hi631/FLEX09/moni09/basic.asm

ROMBASE   EQU  $E000
UART      EQU  $FFD0
RECEV     EQU  UART+1
TRANS     EQU  UART+1
USTAT     EQU  UART
UCTRL     EQU  UART
RTS_LOW   EQU  $15

BS        EQU  8              BACKSPACE
CR        EQU  $D             ENTER KEY
ESC       EQU  $1B            ESCAPE CODE
SPACE     EQU  $20            SPACE (BLANK)
STKBUF    EQU  58             STACK BUFFER ROOM
LBUFMX    EQU  250            MAX NUMBER OF CHARS IN A BASIC LINE
MAXLIN    EQU  $FA            MAXIMUM MS BYTE OF LINE NUMBER
* PSEUDO OPS
SKP1      EQU  $21            OP CODE OF BRN    - SKIP ONE BYTE
SKP2      EQU  $8C            OP CODE OF CMPX # - SKIP TWO BYTES
SKP1LD    EQU  $86            OP CODE OF LDA #  - SKIP THE NEXT BYTE AND
*                             LOAD THE VALUE OF THAT BYTE INTO ACCA - USUALLY
*                             USED TO LOAD ACCA WITH A NON-ZERO VALUE

          ORG  0
ENDFLG    RMB  1              STOP/END FLAG: POSITIVE=STOP, NEG=END
CHARAC    RMB  1              TERMINATOR FLAG 1
ENDCHR    RMB  1              TERMINATOR FLAG 2
TMPLOC    RMB  1              SCRATCH VARIABLE
IFCTR     RMB  1              IF COUNTER - HOW MANY IF STATEMENTS IN A LINE
DIMFLG    RMB  1              *DV* ARRAY FLAG 0=EVALUATE, 1=DIMENSIONING
VALTYP    RMB  1              *DV* *PV TYPE FLAG: 0=NUMERIC, $FF=STRING
GARBFL    RMB  1              *TV STRING SPACE HOUSEKEEPING FLAG
ARYDIS    RMB  1              DISABLE ARRAY SEARCH: 00=ALLOW SEARCH
INPFLG    RMB  1              *TV INPUT FLAG: READ=0, INPUT<>0
RELFLG    RMB  1              *TV RELATIONAL OPERATOR FLAG
TEMPPT    RMB  2              *PV TEMPORARY STRING STACK POINTER
LASTPT    RMB  2              *PV ADDR OF LAST USED STRING STACK ADDRESS
TEMPTR    RMB  2              TEMPORARY POINTER
TMPTR1    RMB  2              TEMPORARY DESCRIPTOR STORAGE (STACK SEARCH)
FPA2      RMB  4              FLOATING POINT ACCUMULATOR #2 MANTISSA
BOTSTK    RMB  2              BOTTOM OF STACK AT LAST CHECK
TXTTAB    RMB  2              *PV BEGINNING OF BASIC PROGRAM
VARTAB    RMB  2              *PV START OF VARIABLES
ARYTAB    RMB  2              *PV START OF ARRAYS
ARYEND    RMB  2              *PV END OF ARRAYS (+1)
FRETOP    RMB  2              *PV START OF STRING STORAGE (TOP OF FREE RAM)
STRTAB    RMB  2              *PV START OF STRING VARIABLES
FRESPC    RMB  2              UTILITY STRING POINTER
MEMSIZ    RMB  2              *PV TOP OF STRING SPACE
OLDTXT    RMB  2              SAVED LINE NUMBER DURING A "STOP"
BINVAL    RMB  2              BINARY VALUE OF A CONVERTED LINE NUMBER
OLDPTR    RMB  2              SAVED INPUT PTR DURING A "STOP"
TINPTR    RMB  2              TEMPORARY INPUT POINTER STORAGE
DATTXT    RMB  2              *PV 'DATA' STATEMENT LINE NUMBER POINTER
DATPTR    RMB  2              *PV 'DATA' STATEMENT ADDRESS POINTER
DATTMP    RMB  2              DATA POINTER FOR 'INPUT' & 'READ'
VARNAM    RMB  2              *TV TEMP STORAGE FOR A VARIABLE NAME
VARPTR    RMB  2              *TV POINTER TO A VARIABLE DESCRIPTOR
VARDES    RMB  2              TEMP POINTER TO A VARIABLE DESCRIPTOR
RELPTR    RMB  2              POINTER TO RELATIONAL OPERATOR PROCESSING ROUTINE
TRELFL    RMB  1              TEMPORARY RELATIONAL OPERATOR FLAG BYTE
* FLOATING POINT ACCUMULATORS #3,4 & 5 ARE MOSTLY
* USED AS SCRATCH PAD VARIABLES.
** FLOATING POINT ACCUMULATOR #3 :PACKED: ($40-$44)
V40       RMB  1
V41       RMB  1
V42       RMB  1
V43       RMB  1
V44       RMB  1
** FLOATING POINT ACCUMULATOR #4 :PACKED: ($45-$49)
V45       RMB  1
V46       RMB  1
V47       RMB  1
V48       RMB  2
** FLOATING POINT ACCUMULATOR #5 :PACKED: ($4A-$4E)
V4A       RMB  1
V4B       RMB  2
V4D       RMB  2
** FLOATING POINT ACCUMULATOR #0
FP0EXP    RMB  1              *PV FLOATING POINT ACCUMULATOR #0 EXPONENT
FPA0      RMB  4              *PV FLOATING POINT ACCUMULATOR #0 MANTISSA
FP0SGN    RMB  1              *PV FLOATING POINT ACCUMULATOR #0 SIGN
COEFCT    RMB  1              POLYNOMIAL COEFFICIENT COUNTER
STRDES    RMB  5              TEMPORARY STRING DESCRIPTOR
FPCARY    RMB  1              FLOATING POINT CARRY BYTE
** FLOATING POINT ACCUMULATOR #1
FP1EXP    RMB  1              *PV FLOATING POINT ACCUMULATOR #1 EXPONENT
FPA1      RMB  4              *PV FLOATING POINT ACCUMULATOR #1 MANTISSA
FP1SGN    RMB  1              *PV FLOATING POINT ACCUMULATOR #1 SIGN
RESSGN    RMB  1              SIGN OF RESULT OF FLOATING POINT OPERATION
FPSBYT    RMB  1              FLOATING POINT SUB BYTE (FIFTH BYTE)
COEFPT    RMB  2              POLYNOMIAL COEFFICIENT POINTER
LSTTXT    RMB  2              CURRENT LINE POINTER DURING LIST
CURLIN    RMB  2              *PV CURRENT LINE # OF BASIC PROGRAM, $FFFF = DIRECT
DEVCFW    RMB  1              *TV TAB FIELD WIDTH
DEVLCF    RMB  1              *TV TAB ZONE
DEVPOS    RMB  1              *TV PRINT POSITION
DEVWID    RMB  1              *TV PRINT WIDTH
RSTFLG    RMB  1              *PV WARM START FLAG: $55=WARM, OTHER=COLD
RSTVEC    RMB  2              *PV WARM START VECTOR - JUMP ADDRESS FOR WARM START
TOPRAM    RMB  2              *PV TOP OF RAM
IKEYIM    RMB  1              *TV INKEY$ RAM IMAGE
ZERO      RMB  2              *PV DUMMY - THESE TWO BYTES ARE ALWAYS ZERO

* THE FOLLOWING BYTES ARE INITIALISED FROM ROM AT LA10D
LPTCFW    RMB  1              16
LPTLCF    RMB  1              112
LPTWID    RMB  1              132
LPTPOS    RMB  1              0
EXECJP    RMB  2              LB4AA

* LINE INPUT ROUTINE IS COPIED TO HERE FROM ROM
GETNCH    RMB  2
          RMB  2
          RMB  2
GETCCH    RMB  1              *PV OP CODE OF LDA EXTENDED
CHARAD    RMB  2              *PV ADDR OF CHAR BEING PROCESSED
          RMB  3              *PV JUMP BACK INTO THE BASIC RUM

VAB       RMB  1              = LOW ORDER FOUR BYTES OF THE PRODUCT
VAC       RMB  1              = OF A FLOATING POINT MULTIPLICATION
VAD       RMB  1              = THESE BYTES ARE USE AS RANDOM DATA
VAE       RMB  1              = BY THE RND STATEMENT

* EXTENDED BASIC VARIABLES
TRCFLG    RMB  1              *PV TRACE FLAG 0=OFF ELSE=ON
USRADR    RMB  2              *PV ADDRESS OF THE START OF USR VECTORS

* EXTENDED BASIC SCRATCH PAD VARIABLES
VCF       RMB  2
VD1       RMB  2
VD3       RMB  2
VD5       RMB  2
VD7       RMB  1
VD8       RMB  1
VD9       RMB  1
VDA       RMB  1
SW3VEC    RMB  3
SW2VEC    RMB  3
SWIVEC    RMB  3
NMIVEC    RMB  3
IRQVEC    RMB  3
FRQVEC    RMB  3
USRJMP    RMB  3              JUMP ADDRESS FOR BASIC'S USR FUNCTION
RVSEED    RMB  1              * FLOATING POINT RANDOM NUMBER SEED EXPONENT
          RMB  4              * MANTISSA: INITIALLY SET TO $804FC75259

**** USR FUNCTION VECTOR ADDRESSES (EX BASIC ONLY)
USR0      RMB  2              USR 0 VECTOR
          RMB  2              USR 1
          RMB  2              USR 2
          RMB  2              USR 3
          RMB  2              USR 4
          RMB  2              USR 5
          RMB  2              USR 6
          RMB  2              USR 7
          RMB  2              USR 8
          RMB  2              USR 9

STRSTK    RMB  8*5            STRING DESCRIPTOR STACK
LINHDR    RMB  2              LINE INPUT BUFFER HEADER
LINBUF    RMB  LBUFMX+1       BASIC LINE INPUT BUFFER
STRBUF    RMB  41             STRING BUFFER

HLOADAD   RMB  2
HLOADDL   RMB  1
HLOADWK   RMB  1

PROGST    RMB  1              START OF PROGRAM SPACE

*         INTERRUPT VECTORS
          ORG  ROMBASE+$1FF2  $FFF2
SWI3      RMB  2
SWI2      RMB  2
FIRQ      RMB  2
IRQ       RMB  2
SWI       RMB  2
NMI       RMB  2
RESETV    RMB  2



          ORG  ROMBASE
*
          JMP  RESVEC
*
H1IN      BSR  CONSIN
          CMPA #$3A
          BGE  H1IN2
          SUBA #$30
          RTS
H1IN2     CMPA #$47
          BGE  H1IN3
          SUBA #$37
          RTS
H1IN3     SUBA #$57
          RTS
HDTIN     BSR  H1IN
          ASLA
          ASLA
          ASLA
          ASLA
          STA  HLOADWK
          BSR  H1IN
          ADDA HLOADWK
          RTS
HLOAD     LDA  #$25           DISPLAY '%'
          BSR  PUTCHR
          BSR  CONSIN
          CMPA #$3A           ? :
          BNE  HLOAD
          BSR  HDTIN          A = DL
          STA  HLOADDL
          BSR  HDTIN
          STA  HLOADAD        ADDRESS
          BSR  HDTIN
          STA  HLOADAD+1
          BSR  HDTIN
          BEQ  HLOAD2         00 = DATA.LINE
          LDA  #$0D
          RTS
HLOAD2    LDX  HLOADAD
          LDB  HLOADDL
HLOAD3    BSR  HDTIN
          STA  ,X+
          DECB
          BNE  HLOAD3
          BSR  HDTIN          SUM(DUMY.READ)
          BSR  CONSIN         CR (DUMY.READ)
          BRA  HLOAD

* CONSOLE IN
LA171
CONSIN    BSR  KEYIN          GET A CHARACTER FROM CONSOLE IN
          BEQ  LA171          LOOP IF NO KEY DOWN
          RTS

*
* THIS ROUTINE GETS A KEYSTROKE FROM THE KEYBOARD IF A KEY
* IS DOWN. IT RETURNS ZERO TRUE IF THERE WAS NO KEY DOWN.
*
*
LA1C1
KEYIN     LDA  USTAT
          BITA #1
          BEQ  NOCHAR
          LDA  RECEV

          CMPA #$0C           Ctrl-L ?
          BNE  KEYIN2
          BSR  HLOAD
          JMP  [HLOADAD]      JMP FLEX.MONITOR
          LDA #$0D
KEYIN2    ANDA #$7F
KEYINR    RTS
NOCHAR    CLRA
          RTS


* CONSOLE OUT
PUTCHR    BSR  WAITACIA
          PSHS A
          CMPA #CR            IS IT CARRIAGE RETURN?
          BEQ  NEWLINE        YES
          STA  TRANS
          INC  LPTPOS         INCREMENT CHARACTER COUNTER
          LDA  LPTPOS         CHECK FOR END OF LINE PRINTER LINE
          CMPA LPTWID         AT END OF LINE PRINTER LINE?
          BLO  PUTEND         NO
NEWLINE   CLR  LPTPOS         RESET CHARACTER COUNTER
          BSR  WAITACIA
          LDA  #13
          STA  TRANS
          BSR  WAITACIA
          LDA  #10            DO LINEFEED AFTER CR
          STA  TRANS
PUTEND    PULS A
          RTS

WAITACIA  PSHS A
WRWAIT    LDA  USTAT
          BITA #2
          BEQ  WRWAIT
          PULS A
          RTS

* COME HERE FROM RESET
RESVEC
LA00E     LDS  #LINBUF+LBUFMX+1 SET STACK TO TOP OF LINE INPUT BUFFER
          LDA  RSTFLG         GET WARM START FLAG
          CMPA #$55+1           IS IT A WARM START?
          BNE  BACDST         NO - D0 A COLD START
          LDX  RSTVEC         WARM START VECTOR
          LDA  ,X             GET FIRST BYTE OF WARM START ADDR
          CMPA #$12           IS IT NOP?
          BNE  BACDST         NO - DO A COLD START
          JMP  ,X             YES, G0 THERE

* COLD START ENTRY

BACDST    LDX  #PROGST+1      POINT X TO CLEAR 1ST 1K OF RAM
LA077     CLR  ,--X           MOVE POINTER DOWN TWO-CLEAR BYTE
          LEAX 1,X            ADVANCE POINTER ONE
          BNE  LA077          KEEP GOING IF NOT AT BOTTOM OF PAGE 0
          LDX  #PROGST        SET TO START OF PROGRAM SPACE
          CLR  ,X+            CLEAR 1ST BYTE OF BASIC PROGRAM
          STX  TXTTAB         BEGINNING OF BASIC PROGRAM
LA084     LDA  2,X            LOOK FOR END OF MEMORY
          COMA                * COMPLEMENT IT AND PUT IT BACK
          STA  2,X            * INTO SYSTEM MEMORY
          CMPA 2,X            IS IT RAM?
          BNE  LA093          BRANCH IF NOT (ROM, BAD RAM OR NO RAM)
          LEAX 1,X            MOVE POINTER UP ONE
          COM  1,X            RE-COMPLEMENT TO RESTORE BYTE
          BRA  LA084          KEEP LOOKING FOR END OF RAM
LA093     STX  TOPRAM         SAVE ABSOLUTE TOP OF RAM
          STX  MEMSIZ         SAVE TOP OF STRING SPACE
          STX  STRTAB         SAVE START OF STRING VARIABLES
          LEAX -200,X         CLEAR 200 - DEFAULT STRING SPACE TO 200 BYTES
          STX  FRETOP         SAVE START OF STRING SPACE
          TFR  X,S            PUT STACK THERE
          LDX  #LA10D         POINT X TO ROM SOURCE DATA
          LDU  #LPTCFW        POINT U TO RAM DESTINATION
          LDB  #18            MOVE 18 BYTES
          JSR  LA59A          MOVE 18 BYTES FROM ROM TO RAM
          LDU  #IRQVEC        POINT U TO NEXT RAM DESTINATION
          LDB  #4             MOVE 4 MORE BYTES
          JSR  LA59A          MOVE 4 BYTES FROM ROM TO RAM
          LDA  #$39
          STA  LINHDR-1       PUT RTS IN LINHDR-1
          JSR  LAD19          G0 DO A "NEW"
* EXTENDED BASIC INITIALISATION
          LDX  #USR0          INITIALIZE ADDRESS OF START OF
          STX  USRADR         USR JUMP TABLE
* INITIALIZE THE USR CALLS TO "FC ERROR"
          LDU  #LB44A         ADDRESS OF "FC ERROR" ROUTINE
          LDB  #10            10 USR CALLS IN EX BASIC
L8031     STU  ,X++           STORE "FC" ERROR AT USR ADDRESSES
          DECB                FINISHED ALL 10?
          BNE  L8031          NO

* INITIALISE ACIA
          LDA  #RTS_LOW       DIV16 CLOCK -> 7372800 / 4 / 16 = 115200
          STA  UCTRL
          LDX  #LA147-1       POINT X TO COLOR BASIC COPYRIGHT MESSAGE
          JSR  LB99C          PRINT "COLOR BASIC"
          LDX  #BAWMST        WARM START ADDRESS
          STX  RSTVEC         SAVE IT
          LDA  #$55           WARM START FLAG
          STA  RSTFLG         SAVE IT
          BRA  LA0F3          GO TO BASIC'S MAIN LOOP
BAWMST    NOP                 NOP REQ'D FOR WARM START
          JSR  LAD33          DO PART OF A NEW
LA0F3     JMP  LAC73          GO TO MAIN LOOP OF BASIC
*
* FIRQ SERVICE ROUTINE
BFRQSV
          RTI
*
* THESE BYTES AND THE LINE INPUT ROUTINE ARE MOVED TO
* ADDRESSES $76-$87 (18 BYTES)
LA10D     FCB  16             TAB FIELD WIDTH
          FCB  64             LAST TAB ZONE
          FCB  255            PRINTER WIDTH
          FCB  0              LINE PRINTER POSITION
          FDB  LB44A          ARGUMENT OF EXEC COMMAND - SET TO "FC" ERROR

* LINE INPUT ROUTINE PICKS UP THE NEXT INPUT CHARACTER FROM
* BASIC. THE ADDRESS OF THE NEXT BASIC BYTE TO BE
* INTERPRETED IS STORED AT CHARAD.
          INC  CHARAD+1       *PV INCREMENT LS BYTE OF INPUT POINTER
          BNE  LA123          *PV BRANCH IF NOT ZERO (NO CARRY)
          INC  CHARAD         *PV INCREMENT MS BYTE OF INPUT POINTER
LA123     LDA  >0000          *PV THE 0000 WILL CONTAIN THE ADDRESS OF
*                             *PV THE CURRENT CHARACTER THAT THE BASIC
*                             *PV INTERPRETER IS PROCESSING
          JMP  BROMHK         *PV JUMP BACK INTO THE BASIC ROM

* THESE BYTES ARE MOVED TO ADDRESSES $A7-$B4 (NAC: ACTUALLY THEY ARE NOT..)
          JMP  BIRQSV         IRQ SERVICE
          JMP  BFRQSV         FIRQ SERVICE
          JMP  LB44A          USR ADDRESS FOR 8K BASIC (INITIALIZED TO "FC" ERROR)
          FCB  $80            *RANDOM SEED
          FDB  $4FC7          *RANDON SEED OF MANTISSA
          FDB  $5259          *.811635157
* BASIC COMMAND INTERPRETATION TABLE ROM IMAGE
COMVEC    FCB  50             50 BASIC COMMANDS
          FDB  LAA66          POINTS TO RESERVED WORDS
          FDB  LAB67          POINTS TO JUMP TABLE FOR COMMANDS
          FCB  29             29 BASIC SECONDARY COMMANDS
          FDB  LAB1A          POINTS TO SECONDARY FUNCTION RESERVED WORDS
          FDB  LAA29          POINTS TO SECONDARY FUNCTION JUMP TABLE
          FDB  0              NO MORE TABLES (RES WORDS=0)
          FDB  0              NO MORE TABLES
          FDB  0              NO MORE TABLES
          FDB  0              NO MORE TABLES
          FDB  0              NO MORE TABLES
          FDB  0              NO MORE TABLES (SECONDARY FNS =0)

* COPYRIGHT MESSAGES
LA147     FCC  "6809 EXTENDED BASIC"
          FCB  CR
          FCC  "(C) 1982 BY MICROSOFT"
LA156     FCB  CR,CR
LA165     FCB  $00


LA35F     PSHS X,B,A          SAVE REGISTERS
          LDX  LPTCFW         TAB FIELD WIDTH AND TAB ZONE
          LDD  LPTWID         PRINTER WIDTH AND POSITION
LA37C     STX  DEVCFW         SAVE TAB FIELD WIDTH AND ZONE
          STB  DEVPOS         SAVE PRINT POSITION
          STA  DEVWID         SAVE PRINT WIDTH
          PULS A,B,X,PC       RESTORE REGISTERS

* THIS IS THE ROUTINE THAT GETS AN INPUT LINE FOR BASIC
* EXIT WITH BREAK KEY: CARRY = 1
* EXIT WITH ENTER KEY: CARRY = 0
LA38D
LA390     CLR  IKEYIM         RESET BREAK CHECK KEY TEMP KEY STORAGE
          LDX  #LINBUF+1      INPUT LINE BUFFER
          LDB  #1             ACCB CHAR COUNTER: SET TO 1 TO ALLOW A
*         BACKSPACE AS FIRST CHARACTER
LA39A     JSR  LA171          GO GET A CHARACTER FROM CONSOLE IN
          CMPA #BS            BACKSPACE
          BNE  LA3B4          NO
          DECB                YES - DECREMENT CHAR COUNTER
          BEQ  LA390          BRANCH IF BACK AT START OF LINE AGAIN
          LEAX -1,X           DECREMENT BUFFER POINTER
          BRA  LA3E8          ECHO CHAR TO SCREEN
LA3B4     CMPA #$15           SHIFT RIGHT ARROW?
          BNE  LA3C2          NO
* YES, RESET BUFFER TO BEGINNING AND ERASE CURRENT LINE
LA3B8     DECB                DEC CHAR CTR
          BEQ  LA390          GO BACK TO START IF CHAR CTR = 0
          LDA  #BS            BACKSPACE?
          JSR  PUTCHR         SEND TO CONSOLE OUT (SCREEN)
          BRA  LA3B8          KEEP GOING
LA3C2     CMPA #3             BREAK KEY?
          ORCC #1             SET CARRY FLAG
          BEQ  LA3CD          BRANCH IF BREAK KEY DOWN
LA3C8     CMPA #CR            ENTER KEY?
          BNE  LA3D9          NO
LA3CC     CLRA                CLEAR CARRY FLAG IF ENTER KEY - END LINE ENTRY
LA3CD     PSHS CC             SAVE CARRY FLAG
          JSR  LB958          SEND CR TO SCREEN
          CLR  ,X             MAKE LAST BYTE IN INPUT BUFFER = 0
          LDX  #LINBUF        RESET INPUT BUFFER POINTER
          PULS CC,PC          RESTORE CARRY FLAG

* INSERT A CHARACTER INTO THE BASIC LINE INPUT BUFFER
LA3D9     CMPA #$20           IS IT CONTROL CHAR?
          BLO  LA39A          BRANCH IF CONTROL CHARACTER
          CMPA #'z+1          *
          BCC  LA39A          * IGNORE IF > LOWER CASE Z
          CMPB #LBUFMX        HAVE 250 OR MORE CHARACTERS BEEN ENTERED?
          BCC  LA39A          YES, IGNORE ANY MORE
          STA  ,X+            PUT IT IN INPUT BUFFER
          INCB                INCREMENT CHARACTER COUNTER
LA3E8     JSR  PUTCHR         ECHO IT TO SCREEN
          BRA  LA39A          GO SET SOME MORE


* EXEC
EXEC      BEQ  LA545          BRANCH IF NO ARGUMENT
          JSR  LB73D          EVALUATE ARGUMENT - ARGUMENT RETURNED IN X
          STX  EXECJP         STORE X TO EXEC JUMP ADDRESS
LA545     JMP  [EXECJP]       GO DO IT

* BREAK CHECK
LA549     JMP  LADEB          GO DO BREAK KEY CHECK

* INKEY$
INKEY     LDA  IKEYIM         WAS A KEY DOWN IN THE BREAK CHECK?
          BNE  LA56B          YES
          JSR  KEYIN          GO GET A KEY
LA56B     CLR  IKEYIM         CLEAR INKEY RAM IMAGE
          STA  FPA0+3         STORE THE KEY IN FPA0
          LBNE LB68F          CONVERT FPA0+3 TO A STRING
          STA  STRDES         SET LENGTH OF STRING = 0 IF NO KEY DOWN
          JMP  LB69B          PUT A NULL STRING ONTO THE STRING STACK

* MOVE ACCB BYTES FROM (X) TO (U)
LA59A     LDA  ,X+            GET BYTE FROM X
          STA  ,U+            STORE IT AT U
          DECB                MOVED ALL BYTES?
          BNE  LA59A          NO
LA5A1     RTS

LA5C4     RTS

** THIS ROUTINE WILL SCAN OFF THE FILE NAME FROM A BASIC LINE
** AND RETURN A SYNTAX ERROR IF THERE ARE ANY CHARACTERS
** FOLLOWING THE END OF THE NAME
LA5C7     JSR  GETCCH         GET CURRENT INPUT CHAR FROM BASIC LINE
LA5C9     BEQ  LA5C4          RETURN IF END OF LINE
          JMP  LB277          SYNTAX ERROR IF ANY MORE CHARACTERS
* IRQ SERVICE
BIRQSV
LA9C5     RTI  RETURN FROM INTERRUPT

* SET CARRY IF NUMERIC - RETURN WITH
* ZERO FLAG SET IF ACCA = 0 OR 3A(:) - END
* OF BASIC LINE OR SUB LINE
BROMHK    CMPA #'9+1          IS THIS CHARACTER >=(ASCII 9)+1?
          BHS  LAA28          BRANCH IF > 9; Z SET IF = COLON
          CMPA #SPACE         SPACE?
          BNE  LAA24          NO - SET CARRY IF NUMERIC
          JMP  GETNCH         IF SPACE, GET NECT CHAR (IGNORE SPACES)
LAA24     SUBA #'0            * SET CARRY IF
          SUBA #-'0           * CHARACTER > ASCII 0
LAA28     RTS

* DISPATCH TABLE FOR SECONDARY FUNCTIONS
* TOKENS ARE PRECEEDED BY $FF
* FIRST SET ALWAYS HAS ONE PARAMETER
FUNC_TAB
LAA29     FDB  SGN            SGN
          FDB  INT            INT
          FDB  ABS            ABS
          FDB  USRJMP         USR
TOK_USR   EQU  *-FUNC_TAB/2+$7F
TOK_FF_USR EQU  *-FUNC_TAB/2+$FF7F
          FDB  RND            RND
          FDB  SIN            SIN
          FDB  PEEK           PEEK
          FDB  LEN            LEN
          FDB  STR            STR$
          FDB  VAL            VAL
          FDB  ASC            ASC
          FDB  CHR            CHR$
          FDB  ATN            ATN
          FDB  COS            COS
          FDB  TAN            TAN
          FDB  EXP            EXP
          FDB  FIX            FIX
          FDB  LOG            LOG
          FDB  POS            POS
          FDB  SQR            SQR
          FDB  HEXDOL         HEX$
* LEFT, RIGHT AND MID ARE TREATED SEPARATELY
          FDB  LEFT           LEFT$
TOK_LEFT  EQU  *-FUNC_TAB/2+$7F
          FDB  RIGHT          RIGHT$
          FDB  MID            MID$
TOK_MID   EQU  *-FUNC_TAB/2+$7F
* REMAINING FUNCTIONS
          FDB  INKEY          INKEY$
TOK_INKEY EQU  *-FUNC_TAB/2+$7F
          FDB  MEM            MEM
          FDB  VARPT          VARPTR
          FDB  INSTR          INSTR
          FDB  STRING         STRING$
NUM_SEC_FNS EQU  *-FUNC_TAB/2

* THIS TABLE CONTAINS PRECEDENCES AND DISPATCH ADDRESSES FOR ARITHMETIC
* AND LOGICAL OPERATORS - THE NEGATION OPERATORS DO NOT ACT ON TWO OPERANDS
* S0 THEY ARE NOT LISTED IN THIS TABLE. THEY ARE TREATED SEPARATELY IN THE
* EXPRESSION EVALUATION ROUTINE. THEY ARE:
* UNARY NEGATION (-), PRECEDENCE &7D AND LOGICAL NEGATION (NOT), PRECEDENCE $5A
* THE RELATIONAL OPERATORS < > = ARE ALSO NOT LISTED, PRECEDENCE $64.
* A PRECEDENCE VALUE OF ZERO INDICATES END OF EXPRESSION OR PARENTHESES
*
LAA51     FCB  $79
          FDB  LB9C5          +
          FCB  $79
          FDB  LB9BC          -
          FCB  $7B
          FDB  LBACC          *
          FCB  $7B
          FDB  LBB91          /
          FCB  $7F
          FDB  L8489          EXPONENTIATION
          FCB  $50
          FDB  LB2D5          AND
          FCB  $46
          FDB  LB2D4          OR

* THIS IS THE RESERVED WORD TABLE
* FIRST PART OF THE TABLE CONTAINS EXECUTABLE COMMANDS
LAA66     FCC  "FO"           80
          FCB  $80+'R'
          FCC  "G"            81
          FCB  $80+'O'
TOK_GO    EQU  $81
          FCC  "RE"           82
          FCB  $80+'M'
          FCB  ''+$80         83
          FCC  "ELS"          84
          FCB  $80+'E'
          FCC  "I"            85
          FCB  $80+'F'
          FCC  "DAT"          86
          FCB  $80+'A'
          FCC  "PRIN"         87
          FCB  $80+'T'
          FCC  "O"            88
          FCB  $80+'N'
          FCC  "INPU"         89
          FCB  $80+'T'
          FCC  "EN"           8A
          FCB  $80+'D'
          FCC  "NEX"          8B
          FCB  $80+'T'
          FCC  "DI"           8C
          FCB  $80+'M'
          FCC  "REA"          8D
          FCB  $80+'D'
          FCC  "RU"           8E
          FCB  $80+'N'
          FCC  "RESTOR"       8F
          FCB  $80+'E'
          FCC  "RETUR"        90
          FCB  $80+'N'
          FCC  "STO"          91
          FCB  $80+'P'
          FCC  "POK"          92
          FCB  $80+'E'
          FCC  "CON"          93
          FCB  $80+'T'
          FCC  "LIS"          94
          FCB  $80+'T'
          FCC  "CLEA"         95
          FCB  $80+'R'
          FCC  "NE"           96
          FCB  $80+'W'
          FCC  "EXE"          97
          FCB  $80+'C'
          FCC  "TRO"          98
          FCB  $80+'N'
          FCC  "TROF"         99
          FCB  $80+'F'
          FCC  "DE"           9A
          FCB  $80+'L'
          FCC  "DE"           9B
          FCB  $80+'F'
          FCC  "LIN"          9C
          FCB  $80+'E'
          FCC  "RENU"         9D
          FCB  $80+'M'
          FCC  "EDI"          9E
          FCB  $80+'T'
* END OF EXECUTABLE COMMANDS. THE REMAINDER OF THE TABLE ARE NON-EXECUTABLE TOKENS
          FCC  "TAB"          9F
          FCB  $80+'('
TOK_TAB   EQU  $9F
          FCC  "T"            A0
          FCB  $80+'O'
TOK_TO    EQU  $A0
          FCC  "SU"           A1
          FCB  $80+'B'
TOK_SUB   EQU  $A1
          FCC  "THE"          A2
          FCB  $80+'N'
TOK_THEN  EQU  $A2
          FCC  "NO"           A3
          FCB  $80+'T'
TOK_NOT   EQU  $A3
          FCC  "STE"          A4
          FCB  $80+'P'
TOK_STEP  EQU  $A4
          FCC  "OF"           A5
          FCB  $80+'F'
          FCB  '++$80         A6
TOK_PLUS  EQU  $A6
          FCB  '-+$80         A7
TOK_MINUS EQU  $A7
          FCB  '*+$80         A8
          FCB  '/+$80         A9
          FCB  '^+$80         AA
          FCC  "AN"           AB
          FCB  $80+'D'
          FCC  "O"            AC
          FCB  $80+'R'
          FCB  '>+$80         AD
TOK_GREATER EQU  $AD
          FCB  '=+$80         AE
TOK_EQUALS EQU  $AE
          FCB  '<+$80         AF
          FCC  "F"            B0
          FCB  $80+'N'
TOK_FN    EQU  $B0
          FCC  "USIN"         B1
          FCB  $80+'G'
*

* FIRST SET ALWAYS HAS ONE PARAMETER
LAB1A     FCC  "SG"           80
          FCB  $80+'N'
          FCC  "IN"           81
          FCB  $80+'T'
          FCC  "AB"           82
          FCB  $80+'S'
          FCC  "US"           83
          FCB  $80+'R'
          FCC  "RN"           84
          FCB  $80+'D'
          FCC  "SI"           85
          FCB  $80+'N'
          FCC  "PEE"          86
          FCB  $80+'K'
          FCC  "LE"           87
          FCB  $80+'N'
          FCC  "STR"          88
          FCB  $80+'$'
          FCC  "VA"           89
          FCB  $80+'L'
          FCC  "AS"           8A
          FCB  $80+'C'
          FCC  "CHR"          8B
          FCB  $80+'$'
          FCC  "AT"           8C
          FCB  $80+'N'
          FCC  "CO"           8D
          FCB  $80+'S'
          FCC  "TA"           8E
          FCB  $80+'N'
          FCC  "EX"           8F
          FCB  $80+'P'
          FCC  "FI"           90
          FCB  $80+'X'
          FCC  "LO"           91
          FCB  $80+'G'
          FCC  "PO"           92
          FCB  $80+'S'
          FCC  "SQ"           93
          FCB  $80+'R'
          FCC  "HEX"          94
          FCB  $80+'$'
* LEFT, RIGHT AND MID ARE TREATED SEPARATELY
          FCC  "LEFT"         95
          FCB  $80+'$'
          FCC  "RIGHT"        96
          FCB  $80+'$'
          FCC  "MID"          97
          FCB  $80+'$'
* REMAINING FUNCTIONS
          FCC  "INKEY"        98
          FCB  $80+'$'
          FCC  "ME"           99
          FCB  $80+'M'
          FCC  "VARPT"        9A
          FCB  $80+'R'
          FCC  "INST"         9B
          FCB  $80+'R'
          FCC  "STRING"       9C
          FCB  $80+'$'

*
* DISPATCH TABLE FOR COMMANDS TOKEN #
CMD_TAB
LAB67     FDB  FOR             80
          FDB  GO              81
          FDB  REM             82
TOK_REM   EQU  *-CMD_TAB/2+$7F
          FDB  REM             83 (')
TOK_SNGL_Q EQU  *-CMD_TAB/2+$7F
          FDB  REM             84 (ELSE)
TOK_ELSE  EQU  *-CMD_TAB/2+$7F
          FDB  IF              85
TOK_IF    EQU  *-CMD_TAB/2+$7F
          FDB  DATA            86
TOK_DATA  EQU  *-CMD_TAB/2+$7F
          FDB  PRINT           87
TOK_PRINT EQU  *-CMD_TAB/2+$7F
          FDB  ON              88
          FDB  INPUT           89
TOK_INPUT EQU  *-CMD_TAB/2+$7F
          FDB  END             8A
          FDB  NEXT            8B
          FDB  DIM             8C
          FDB  READ            8D
          FDB  RUN             8E
          FDB  RESTOR         8F
          FDB  RETURN          90
          FDB  STOP            91
          FDB  POKE            92
          FDB  CONT           93
          FDB  LIST            94
          FDB  CLEAR           95
          FDB  NEW             96
          FDB  EXEC           97
          FDB  TRON           98
          FDB  TROFF          99
          FDB  DEL            9A
          FDB  DEF            9B
          FDB  LINE           9C
          FDB  RENUM          9D
          FDB  EDIT           9E
TOK_HIGH_EXEC EQU  *-CMD_TAB/2+$7F

* ERROR MESSAGES AND THEIR NUMBERS AS USED INTERNALLY
LABAF     FCC  "NF"           0 NEXT WITHOUT FOR
          FCC  "SN"           1 SYNTAX ERROR
          FCC  "RG"           2 RETURN WITHOUT GOSUB
          FCC  "OD"           3 OUT OF DATA
          FCC  "FC"           4 ILLEGAL FUNCTION CALL
          FCC  "OV"           5 OVERFLOW
          FCC  "OM"           6 OUT OF MEMORY
          FCC  "UL"           7 UNDEFINED LINE NUMBER
          FCC  "BS"           8 BAD SUBSCRIPT
          FCC  "DD"           9 REDIMENSIONED ARRAY
          FCC  "/0"           10 DIVISION BY ZERO
          FCC  "ID"           11 ILLEGAL DIRECT STATEMENT
          FCC  "TM"           12 TYPE MISMATCH
          FCC  "OS"           13 OUT OF STRING SPACE
          FCC  "LS"           14 STRING TOO LONG
          FCC  "ST"           15 STRING FORMULA TOO COMPLEX
          FCC  "CN"           16 CAN'T CONTINUE
          FCC  "FD"           17 BAD FILE DATA
          FCC  "AO"           18 FILE ALREADY OPEN
          FCC  "DN"           19 DEVICE NUMBER ERROR
          FCC  "IO"           20 I/O ERROR
          FCC  "FM"           21 BAD FILE MODE
          FCC  "NO"           22 FILE NOT OPEN
          FCC  "IE"           23 INPUT PAST END OF FILE
          FCC  "DS"           24 DIRECT STATEMENT IN FILE
* ADDITIONAL ERROR MESSAGES ADDED BY EXTENDED BASIC
L890B     FCC  "UF"           25 UNDEFINED FUNCTION (FN) CALL
L890D     FCC  "NE"           26 FILE NOT FOUND

LABE1     FCC  " ERROR"
          FCB  $00
LABE8     FCC  " IN "
          FCB  $00
LABED     FCB  CR
LABEE     FCC  "OK"
          FCB  CR,$00
LABF2     FCB  CR
          FCC  "BREAK"
          FCB  $00

* SEARCH THE STACK FOR "GOSUB/RETURN" OR "FOR/NEXT" DATA.
* THE "FOR/NEXT" INDEX VARIABLE DESCRIPTOR ADDRESS BEING
* SOUGHT IS STORED IN VARDES. EACH BLOCK OF FOR/NEXT DATA IS 18
* BYTES WITH A $80 LEADER BYTE AND THE GOSUB/RETURN DATA IS 5 BYTES
* WITH AN $A6 LEADER BYTE. THE FIRST NON "FOR/NEXT" DATA
* IS CONSIDERED "GOSUB/RETURN"
LABF9     LEAX 4,S            POINT X TO 3RD ADDRESS ON STACK - IGNORE THE
*         FIRST TWO RETURN ADDRESSES ON THE STACK
LABFB     LDB  #18            18 BYTES SAVED ON STACK FOR EACH "FOR" LOOP
          STX  TEMPTR         SAVE POINTER
          LDA  ,X             GET 1ST BYTE
          SUBA #$80           * CHECK FOR TYPE OF STACK JUMP FOUND
          BNE  LAC1A          * BRANCH IF NOT "FOR/NEXT"
          LDX  1,X            = GET INDEX VARIABLE DESCRIPTOR
          STX  TMPTR1         = POINTER AND SAVE IT IN TMPTR1
          LDX  VARDES         GET INDEX VARIABLE BEING SEARCHED FOR
          BEQ  LAC16          BRANCH IF DEFAULT INDEX VARIABLE - USE THE
*                             FIRST "FOR/NEXT" DATA FOUND ON STACK
*                             IF NO INDEX VARIABLE AFTER "NEXT"
          CMPX TMPTR1         DOES THE STACK INDEX MATCH THE ONE
*                             BEING SEARCHED FOR?
          BEQ  LAC1A          YES
          LDX  TEMPTR         * RESTORE INITIAL POINTER, ADD
          ABX                 * 18 TO IT AND LOOK FOR
          BRA  LABFB          * NEXT BLOCK OF DATA
LAC16     LDX  TMPTR1         = GET 1ST INDEX VARIABLE FOUND AND
          STX  VARDES         = SAVE AS "NEXT" INDEX
LAC1A     LDX  TEMPTR         POINT X TO START OF "FOR/NEXT" DATA
          TSTA                SET ZERO FLAG IF "FOR/NEXT" DATA
          RTS
* CHECK FOR MEMORY SPACE FOR NEW TOP OF
* ARRAYS AND MOVE ARRAYS TO NEW LOCATION
LAC1E     BSR  LAC37          ACCD = NEW BOTTOM OF FREE RAM - IS THERE
*                             ROOM FOR THE STACK?
* MOVE BYTES FROM V43(X) TO V41(U) UNTIL (X) = V47 AND
* SAVE FINAL VALUE OF U IN V45
LAC20     LDU  V41            POINT U TO DESTINATION ADDRESS (V41)
          LEAU 1,U            ADD ONE TO U - COMPENSATE FOR FIRST PSHU
          LDX  V43            POINT X TO SOURCE ADDRESS (V43)
          LEAX 1,X            ADD ONE - COMPENSATE FOR FIRST LDA ,X
LAC28     LDA  ,-X            GRAB A BYTE FROM SOURCE
          PSHU A              MOVE IT TO DESTINATION
          CMPX V47            DONE?
          BNE  LAC28          NO - KEEP MOVING BYTES
          STU  V45            SAVE FINAL DESTINATION ADDRESS
LAC32     RTS
* CHECK TO SEE IF THERE IS ROOM TO STORE 2*ACCB
* BYTES IN FREE RAM - OM ERROR IF NOT
LAC33     CLRA                * ACCD CONTAINS NUMBER OF EXTRA
          ASLB                * BYTES TO PUT ON STACK
          ADDD ARYEND         END OF PROGRAM AND VARIABLES
LAC37     ADDD #STKBUF        ADD STACK BUFFER - ROOM FOR STACK?
          BCS  LAC44          BRANCH IF GREATER THAN $FFFF
          STS  BOTSTK         CURRENT NEW BOTTOM OF STACK STACK POINTER
          CMPD BOTSTK         ARE WE GOING TO BE BELOW STACK?
          BCS  LAC32          YES - NO ERROR
LAC44     LDB  #6*2           OUT OF MEMORY ERROR

* ERROR SERVICING ROUTINE
LAC46     JSR  LAD33          RESET STACK, STRING STACK, CONTINUE POINTER
          JSR  LB95C          SEND A CR TO SCREEN
          JSR  LB9AF          SEND A "?" TO SCREEN
          LDX  #LABAF         POINT TO ERROR TABLE
LAC60     ABX                 ADD MESSAGE NUMBER OFFSET
          BSR  LACA0          * GET TWO CHARACTERS FROM X AND
          BSR  LACA0          * SEND TO CONSOLE OUT (SCREEN)
          LDX  #LABE1-1       POINT TO "ERROR" MESSAGE
LAC68     JSR  LB99C          PRINT MESSAGE POINTED TO BY X
          LDA  CURLIN         GET CURRENT LINE NUMBER (CURL IN)
          INCA                TEST FOR DIRECT MODE
          BEQ  LAC73          BRANCH IF DIRECT MODE
          JSR  LBDC5          PRINT "IN ****"

* THIS IS THE MAIN LOOP OF BASIC WHEN IN DIRECT MODE
LAC73     JSR  LB95C          MOVE CURSOR TO START OF LINE
          LDX  #LABED         POINT X TO "OK", CR MESSAGE
          JSR  LB99C          PRINT "OK", CR
LAC7C     JSR  LA390          GO GET AN INPUT LINE
          LDU  #$FFFF         THE LINE NUMBER FOR DIRECT MODE IS $FFFF
          STU  CURLIN         SAVE IT IN CURLIN
          BCS  LAC7C          BRANCH IF LINE INPUT TERMINATED BY BREAK
          STX  CHARAD         SAVE (X) AS CURRENT INPUT POINTER - THIS WILL
*         ENABLE THE "LIVE KEYBOARD" (DIRECT) MODE. THE
*         LINE JUST ENTERED WILL BE INTERPRETED
          JSR  GETNCH         GET NEXT CHARACTER FROM BASIC
          BEQ  LAC7C          NO LINE INPUT - GET ANOTHER LINE
          BCS  LACA5          BRANCH IF NUMER1C - THERE WAS A LINE NUMBER BEFORE
*         THE  STATEMENT ENTERED, SO THIS STATEMENT
*         WILL BE MERGED INTO THE BASIC PROGRAM
          JSR  LB821          GO CRUNCH LINE
          JMP  LADC0          GO EXECUTE THE STATEMENT (LIVE KEYBOARD)
*
LACA0     LDA  ,X+            GET A CHARACTER
          JMP  LB9B1          SEND TO CONSOLE OUT
* TAKE A LINE FROM THE LINE INPUT BUFFER
* AND INSERT IT INTO THE BASIC PROGRAM
LACA5     JSR  LAF67          CONVERT LINE NUMBER TO BINARY
LACA8     LDX  BINVAL         GET CONVERTED LINE NUMBER
          STX  LINHDR         STORE IT IN LINE INPUT HEADER
          JSR  LB821          GO CRUNCH THE LINE
          STB  TMPLOC         SAVE LINE LENGTH
          BSR  LAD01          FIND OUT WHERE TO INSERT LINE
          BCS  LACC8          BRANCH IF LINE NUMBER DOES NOT ALREADY EXIST
          LDD  V47            GET ABSOLUTE ADDRESS OF LINE NUMBER
          SUBD ,X             SUBTRACT ADDRESS OF NEXT LINE NUMBER
          ADDD VARTAB         * ADD TO CURRENT END OF PROGRAM - THIS WILL REMOVE
          STD  VARTAB         * THE LENGTH OF THIS LINE NUMBER FROM THE PROGRAM
          LDU  ,X             POINT U TO ADDRESS OF NEXT LINE NUMBER
* DELETE OLD LINE FROM BASIC PROGRAM
LACC0     PULU A              GET A BYTE FROM WHAT'S LEFT OF PROGRAM
          STA  ,X+            MOVE IT DOWN
          CMPX VARTAB         COMPARE TO END OF BASIC PROGRAM
          BNE  LACC0          BRANCH IF NOT AT END
LACC8     LDA  LINBUF         * CHECK TO SEE IF THERE IS A LINE IN
          BEQ  LACE9          * THE BUFFER AND BRANCH IF NONE
          LDD  VARTAB         = SAVE CURRENT END OF
          STD  V43            = PROGRAM IN V43
          ADDB TMPLOC         * ADD LENGTH OF CRUNCHED LINE,
          ADCA #0             * PROPOGATE CARRY AND SAVE NEW END
          STD  V41            * OF PROGRAM IN V41
          JSR  LAC1E          = MAKE SURE THERE'S ENOUGH RAM FOR THIS
*         =    LINE & MAKE A HOLE IN BASIC FOR NEW LINE
          LDU  #LINHDR-2      POINT U TO LINE TO BE INSERTED
LACDD     PULU A              GET A BYTE FROM NEW LINE
          STA  ,X+            INSERT IT IN PROGRAM
          CMPX V45            * COMPARE TO ADDRESS OF END OF INSERTED
          BNE  LACDD          * LINE AND BRANCH IF NOT DONE
          LDX  V41            = GET AND SAVE
          STX  VARTAB         = END OF PROGRAM
LACE9     BSR  LAD21          RESET INPUT POINTER, CLEAR VARIABLES, INITIALIZE
          BSR  LACEF          ADJUST START OF NEXT LINE ADDRESSES
          BRA  LAC7C          REENTER BASIC'S INPUT LOOP
* COMPUTE THE START OF NEXT LINE ADDRESSES FOR THE BASIC PROGRAM
LACEF     LDX  TXTTAB         POINT X TO START OF PROGRAM
LACF1     LDD  ,X             GET ADDRESS OF NEXT LINE
          BEQ  LAD16          RETURN IF END OF PROGRAM
          LEAU 4,X            POINT U TO START OF BASIC TEXT IN LINE
LACF7     LDA  ,U+            * SKIP THROUGH THE LINE UNTIL A
          BNE  LACF7          * ZERO (END OF LINE) IS FOUND
          STU  ,X             SAVE THE NEW START OF NEXT LINE ADDRESS
          LDX  ,X             POINT X TO START OF NEXT LINE
          BRA  LACF1          KEEP GOING
*
* FIND A LINE NUMBER IN THE BASIC PROGRAM
* RETURN WITH CARRY SET IF NO MATCH FOUND
LAD01     LDD  BINVAL         GET THE LINE NUMBER TO FIND
          LDX  TXTTAB         BEGINNING OF PROGRAM
LAD05     LDU  ,X             GET ADDRESS OF NEXT LINE NUMBER
          BEQ  LAD12          BRANCH IF END OF PROG
          CMPD 2,X            IS IT A MATCH?
          BLS  LAD14          CARRY SET IF LOWER; CARRY CLEAR IF MATCH
          LDX  ,X             X = ADDRESS OF NEXT LINE
          BRA  LAD05          KEEP LOOPING FOR LINE NUMBER
LAD12     ORCC #1             SET CARRY FLAG
LAD14     STX  V47            SAVE MATCH LINE NUMBER OR NUMBER OF LINE JUST AFTER
*                             WHERE IT SHOULD HAVE BEEN
LAD16     RTS

* NEW
NEW       BNE  LAD14          BRANCH IF ARGUMENT GIVEN
LAD19     LDX  TXTTAB         GET START OF BASIC
          CLR  ,X+            * PUT 2 ZERO BYTES THERE - ERASE
          CLR  ,X+            * THE BASIC PROGRAM
          STX  VARTAB         AND THE NEXT ADDRESS IS NOW THE END OF PROGRAM
LAD21     LDX  TXTTAB         GET START OF BASIC
          JSR  LAEBB          PUT INPUT POINTER ONE BEFORE START OF BASIC
* ERASE ALL VARIABLES
LAD26     LDX  MEMSIZ         * RESET START OF STRING VARIABLES
          STX  STRTAB         * TO TOP OF STRING SPACE
          JSR  RESTOR         RESET "DATA" POINTER TO START OF BASIC
          LDX  VARTAB         * GET START OF VARIABLES AND USE IT
          STX  ARYTAB         * TO RESET START OF ARRAYS
          STX  ARYEND         RESET END OF ARRAYS
LAD33     LDX  #STRSTK        * RESET STRING STACK POINTER TO
          STX  TEMPPT         * BOTTOM OF STRING STACK
          LDX  ,S             GET RETURN ADDRESS OFF STACK
          LDS  FRETOP         RESTORE STACK POINTER
          CLR  ,-S            PUT A ZERO BYTE ON STACK - TO CLEAR ANY RETURN OF
*                             FOR/NEXT DATA FROM THE STACK
          CLR  OLDPTR         RESET "CONT" ADDRESS SO YOU
          CLR  OLDPTR+1       "CAN'T CONTINUE"
          CLR  ARYDIS         CLEAR THE ARRAY DISABLE FLAG
          JMP  ,X             RETURN TO CALLING ROUTINE - THIS IS NECESSARY
*                             SINCE THE STACK WAS RESET
*
* FOR
*
* THE FOR COMMAND WILL STORE 18 BYTES ON THE STACK FOR
* EACH FOR-NEXT LOOP WHICH IS BEING PROCESSED. THESE
* BYTES ARE DEFINED AS FOLLOWS: 0- $80 (FOR FLAG);
*         1,2=INDEX VARIABLE DESCRIPTOR POINTER; 3-7=FP VALUE OF STEP;
*         8=STEP DIRECTION: $FF IF NEGATIVE; 0 IF ZERO; 1 IF POSITIVE;
* 9-13=FP VALUE OF "TO" PARAMETER;
* 14,15=CURRENT LINE NUMBER; 16,17=RAM ADDRESS OF THE END
*         OF   THE LINE CONTAINING THE "FOR" STATEMENT
FOR       LDA  #$80           * SAVE THE DISABLE ARRAY FLAG IN VO8
          STA  ARYDIS         * DO NOT ALLOW THE INDEX VARIABLE TO BE AN ARRAY
          JSR  LET            SET INDEX VARIABLE TO INITIAL VALUE
          JSR  LABF9          SEARCH THE STACK FOR "FOR/NEXT" DATA
          LEAS 2,S            PURGE RETURN ADDRESS OFF OF THE STACK
          BNE  LAD59          BRANCH IF INDEX VARIABLE NOT ALREADY BEING USED
          LDX  TEMPTR         GET (ADDRESS + 18) OF MATCHED "FOR/NEXT" DATA
          LEAS B,X            MOVE THE STACK POINTER TO THE BEGINNING OF THE
* MATCHED "FOR/NEXT" DATA SO THE NEW DATA WILL
* OVERLAY THE OLD DATA. THIS WILL ALSO DESTROY
* ALL OF THE "RETURN" AND "FOR/NEXT" DATA BELOW
* THIS POINT ON THE STACK
LAD59     LDB  #$09           * CHECK FOR ROOM FOR 18 BYTES
          JSR  LAC33          * IN FREE RAM
          JSR  LAEE8          GET ADDR OF END OF SUBLINE IN X
          LDD  CURLIN         GET CURRENT LINE NUMBER
          PSHS X,B,A          SAVE LINE ADDR AND LINE NUMBER ON STACK
          LDB  #TOK_TO        TOKEN FOR "TO"
          JSR  LB26F          SYNTAX CHECK FOR "TO"
          JSR  LB143          "TM" ERROR IF INDEX VARIABLE SET TO STRING
          JSR  LB141          EVALUATE EXPRESSION
*
          LDB  FP0SGN         GET FPA0 MANTISSA SIGN
          ORB  #$7F           FORM A MASK TO SAVE DATA BITS OF HIGH ORDER MANTISSA
          ANDB FPA0           PUT THE MANTISSA SIGN IN BIT 7 OF HIGH ORDER MANTISSA
          STB  FPA0           SAVE THE PACKED HIGH ORDER MANTISSA
          LDY  #LAD7F         LOAD FOLLOWING ADDRESS INTO Y AS A RETURN
          JMP  LB1EA          ADDRESS - PUSH FPA0 ONTO THE STACK
LAD7F     LDX  #LBAC5         POINT X TO FLOATING POINT NUMBER 1.0 (DEFAULT STEP VALUE)
          JSR  LBC14          MOVE (X) TO FPA0
          JSR  GETCCH         GET CURRENT INPUT CHARACTER
          CMPA #TOK_STEP      STEP TOKEN
          BNE  LAD90          BRANCH IF NO "STEP" VALUE
          JSR  GETNCH         GET A CHARACTER FROM BASIC
          JSR  LB141          EVALUATE NUMERIC EXPRESSION
LAD90     JSR  LBC6D          CHECK STATUS OF FPA0
          JSR  LB1E6          SAVE STATUS AND FPA0 ON THE STACK
          LDD  VARDES         * GET DESCRIPTOR POINTER FOR THE "STEP"
          PSHS B,A            * VARIABLE AND SAVE IT ON THE STACK
          LDA  #$80           = GET THE "FOR" FLAG AND
          PSHS A              = SAVE IT ON THE STACK
*
* MAIN COMMAND INTERPRETATION LOOP
LAD9E     ANDCC #$AF           ENABLE IRQ,FIRQ
          BSR  LADEB          CHECK FOR KEYBOARD BREAK
          LDX  CHARAD         GET BASIC'S INPUT POINTER
          STX  TINPTR         SAVE IT
          LDA  ,X+            GET CURRENT INPUT CHAR & MOVE POINTER
          BEQ  LADB4          BRANCH IF END OF LINE
          CMPA #':            CHECK FOR LINE SEPARATOR
          BEQ  LADC0          BRANCH IF COLON
LADB1     JMP  LB277          "SYNTAX ERROR"-IF NOT LINE SEPARATOR
LADB4     LDA  ,X++           GET MS BYTE OF ADDRESS OF NEXT BASIC LINE
          STA  ENDFLG         SAVE IN STOP/END FLAG - CAUSE A STOP IF
*                             NEXT LINE ADDRESS IS < $8000; CAUSE
*                             AN END IF ADDRESS > $8000
          BEQ  LAE15          BRANCH TO "STOP" - END OF PROGRAM
          LDD  ,X+            GET CURRENT LINE NUMBER
          STD  CURLIN         SAVE IN CURLIN
          STX  CHARAD         SAVE ADDRESS OF FIRST BYTE OF LINE
* EXTENDED BASIC TRACE
          LDA  TRCFLG         TEST THE TRACE FLAG
          BEQ  LADC0          BRANCH IF TRACE OFF
          LDA  #$5B           <LEFT HAND MARKER FOR TRON LINE NUMBER
          JSR  PUTCHR         OUTPUT A CHARACTER
          LDA  CURLIN         GET MS BYTE OF LINE NUMBER
          JSR  LBDCC          CONVERT ACCD TO DECIMAL AND PRINT ON SCREEN
          LDA  #$5D           > RIGHT HAND MARKER FOR TRON LINE NUMBER
          JSR  PUTCHR         OUTPUT A CHARACTER
* END OF EXTENDED BASIC TRACE
LADC0     JSR  GETNCH         GET A CHARACTER FROM BASIC
          BSR  LADC6          GO PROCESS COMMAND
          BRA  LAD9E          GO BACK TO MAIN LOOP
LADC6     BEQ  LADEA          RETURN IF END OF LINE (RTS - was BEQ LAE40)
          TSTA                CHECK FOR TOKEN - BIT 7 SET (NEGATIVE)
          LBPL LET            BRANCH IF NOT A TOKEN - GO DO A "LET" WHICH
*                             IS THE "DEFAULT" TOKEN FOR MICROSOFT BASIC
          CMPA #$FF           SECONDARY TOKEN
          BEQ  SECTOK
          CMPA #TOK_HIGH_EXEC SKIPF TOKEN - HIGHEST EXECUTABLE COMMAND IN BASIC
          BHI  LADB1          "SYNTAX ERROR" IF NON-EXECUTABLE TOKEN
          LDX  COMVEC+3       GET ADDRESS OF BASIC'S COMMAND TABLE
LADD4     ASLA                X2 (2 BYTE/JUMP ADDRESS) & DISCARD BIT 7
          TFR  A,B            SAVE COMMAND OFFSET IN ACCB
          ABX                 NON X POINTS TO COMMAND JUMP ADDR
          JSR  GETNCH         GET AN INPUT CHAR
*
* HERE IS WHERE WE BRANCH TO DO A "COMMAND"
          JMP  [,X]           GO DO A COMMAND
SECTOK
* THE ONLY SECONDARY TOKEN THAT CAN ALSO BE AN EXECUTABLE IS
* THE MID$ REPLACEMENT STATEMENT. SO SPECIAL-CASE CHECK DONE HERE
          JSR  GETNCH         GET AN INPUT CHAR
          CMPA #TOK_MID       TOKEN FOR "MID$"
          LBEQ L86D6          PROCESS MID$ REPLACEMENT
          JMP  LB277          SYNTAX ERROR

*
* RESTORE
RESTOR    LDX  TXTTAB         BEGINNING OF PROGRAM ADDRESS
          LEAX -1,X           MOVE TO ONE BYTE BEFORE PROGRAM
LADE8     STX  DATPTR         SAVE NEW DATA POINTER
LADEA     RTS
*
* BREAK CHECK
LADEB     JSR  LA1C1          GET A KEYSTROKE ENTRY
          BEQ  LADFA          RETURN IF NO INPUT
LADF0     CMPA #3             CONTROL C? (BREAK)
          BEQ  STOP           YES
          CMPA #$13           CONTROL S? (PAUSE)
          BEQ  LADFB          YES
          STA  IKEYIM         SAVE KEYSTROKE IN INKEY IMAGE
LADFA     RTS
LADFB     JSR  KEYIN          GET A KEY
          BEQ  LADFB          BRANCH IF NO KEY DOWN
          BRA  LADF0          CONTINUE - DO A BREAK CHECK
*
* END
END       JSR  GETCCH         GET CURRENT INPUT CHAR
          BRA  LAE0B
*
* STOP
STOP      ORCC #$01           SET CARRY FLAG
LAE0B     BNE  LAE40          BRANCH IF ARGUMENT EXISTS
          LDX  CHARAD         * SAVE CURRENT POSITION OF
          STX  TINPTR         * BASIC'S INPUT POINTER
LAE11     ROR  ENDFLG         ROTATE CARRY INTO BIT 7 OF STOP/END FLAG
          LEAS 2,S            PURGE RETURN ADDRESS OFF STACK
LAE15     LDX  CURLIN         GET CURRENT LINE NUMBER
          CMPX #$FFFF         DIRECT MODE?
          BEQ  LAE22          YES
          STX  OLDTXT         SAVE CURRENT LINE NUMBER
          LDX  TINPTR         * GET AND SAVE CURRENT POSITION
          STX  OLDPTR         * OF BASIC'S INPUT POINTER
LAE22
          LDX  #LABF2-1       POINT TO CR, "BREAK" MESSAGE
          TST  ENDFLG         CHECK STOP/END FLAG
          LBPL LAC73          BRANCH TO MAIN LOOP OF BASIC IF END
          JMP  LAC68          PRINT "BREAK AT ####" AND GO TO
*                             BASIC'S MAIN LOOP IF "STOP"

* CONT
CONT      BNE  LAE40          RETURN IF ARGUMENT GIVEN
          LDB  #2*16          "CAN'T CONTINUE" ERROR
          LDX  OLDPTR         GET CONTINUE ADDRESS (INPUT POINTER)
          LBEQ LAC46          "CN" ERROR IF CONTINUE ADDRESS = 0
          STX  CHARAD         RESET BASIC'S INPUT POINTER
          LDX  OLDTXT         GET LINE NUMBER
          STX  CURLIN         RESET CURRENT LINE NUMBER
LAE40     RTS
*
* CLEAR
CLEAR     BEQ  LAE6F          BRANCH IF NO ARGUMENT
          JSR  LB3E6          EVALUATE ARGUMENT
          PSHS B,A            SAVE AMOUNT OF STRING SPACE ON STACK
          LDX  MEMSIZ         GET CURRENT TOP OF CLEARED SPACE
          JSR  GETCCH         GET CURRENT INPUT CHARACTER
          BEQ  LAE5A          BRANCH IF NO NEW TOP OF CLEARED SPACE
          JSR  LB26D          SYNTAX CHECK FOR COMMA
          JSR  LB73D          EVALUATE EXPRESSlON; RETURN VALUE IN X
          LEAX -1,X           X = TOP OF CLEARED SPACE
          CMPX TOPRAM         COMPARE TO TOP OF RAM
          BHI  LAE72          "OM" ERROR IF > TOP OF RAM
LAE5A     TFR  X,D            ACCD = TOP OF CLEARED SPACE
          SUBD ,S++           SUBTRACT OUT AMOUNT OF CLEARED SPACE
          BCS  LAE72          "OM" ERROR IF FREE MEM < 0
          TFR  D,U            U = BOTTOM OF CLEARED SPACE
          SUBD #STKBUF        SUBTRACT OUT STACK BUFFER
          BCS  LAE72          "OM" ERROR IF FREE MEM < 0
          SUBD VARTAB         SUBTRACT OUT START OF VARIABLES
          BCS  LAE72          "OM" ERROR IF FREE MEM < 0
          STU  FRETOP         SAVE NEW BOTTOM OF CLEARED SPACE
          STX  MEMSIZ         SAVE NEW TOP OF CLEARED SPACE
LAE6F     JMP  LAD26          ERASE ALL VARIABLES, INITIALIZE POINTERS, ETC
LAE72     JMP  LAC44          "OM" ERROR
*
* RUN
RUN       JSR  GETCCH         * GET CURRENT INPUT CHARACTER
          LBEQ LAD21          * IF NO LINE NUMBER
          JSR  LAD26          ERASE ALL VARIABLES
          BRA  LAE9F          "GOTO" THE RUN ADDRESS
*
* GO
GO        TFR  A,B            SAVE INPUT CHARACTER IN ACCB
LAE88     JSR  GETNCH         GET A CHARACTER FROM BASIC
          CMPB #TOK_TO        "TO" TOKEN
          BEQ  LAEA4          BRANCH IF GOTO
          CMPB #TOK_SUB       "SUB" TOKEN
          BNE  LAED7          "SYNTAX ERROR" IF NEITHER
          LDB  #3             =ROOM FOR 6
          JSR  LAC33          =BYTES ON STACK?
          LDU  CHARAD         * SAVE CURRENT BASIC INPUT POINTER, LINE
          LDX  CURLIN         * NUMBER AND SUB TOKEN ON STACK
          LDA  #TOK_SUB       *
          PSHS U,X,A          *
LAE9F     BSR  LAEA4          GO DO A "GOTO"
          JMP  LAD9E          JUMP BACK TO BASIC'S MAIN LOOP
* GOTO
LAEA4     JSR  GETCCH         GET CURRENT INPUT CHAR
          JSR  LAF67          GET LINE NUMBER TO BINARY IN BINVAL
          BSR  LAEEB          ADVANCE BASIC'S POINTER TO END OF LINE
          LEAX $01,X          POINT TO START OF NEXT LINE
          LDD  BINVAL         GET THE LINE NUMBER TO RUN
          CMPD CURLIN         COMPARE TO CURRENT LINE NUMBER
          BHI  LAEB6          IF REO'D LINE NUMBER IS > CURRENT LINE NUMBER,
*              DON'T START LOOKING FROM
*              START OF PROGRAM
          LDX  TXTTAB         BEGINNING OF PROGRAM
LAEB6     JSR  LAD05          GO FIND A LINE NUMBER
          BCS  LAED2          'UNDEFINED LINE NUMBER'
LAEBB     LEAX -1,X           MOVE BACK TO JUST BEFORE START OF LINE
          STX  CHARAD         RESET BASIC'S INPUT POINTER
LAEBF     RTS
*
* RETURN
RETURN    BNE  LAEBF          EXIT ROUTINE IF ARGUMENT GIVEN
          LDA  #$FF           * PUT AN ILLEGAL VARIABLE NAME IN FIRST BYTE OF
          STA  VARDES         * VARDES WHICH WILL CAUSE 'FOR/NEXT' DATA ON THE
*              STACK TO BE IGNORED
          JSR  LABF9          CHECK FOR RETURN DATA ON THE STACK
          TFR  X,S            RESET STACK POINTER - PURGE TWO RETURN ADDRESSES
*              FROM THE STACK
          CMPA #TOK_SUB-$80   SUB TOKEN - $80
          BEQ  LAEDA          BRANCH IF 'RETURN' FROM SUBROUTINE
          LDB  #2*2           ERROR #2 'RETURN WITHOUT GOSUB'
          FCB  SKP2           SKIP TWO BYTES
LAED2     LDB  #7*2           ERROR #7 'UNDEFINED LINE NUMBER'
          JMP  LAC46          JUMP TO ERROR HANDLER
LAED7     JMP  LB277          'SYNTAX ERROR'
LAEDA     PULS A,X,U          * RESTORE VALUES OF CURRENT LINE NUMBER AND
          STX  CURLIN         * BASIC'S INPUT POINTER FOR THIS SUBROUTINE
          STU  CHARAD         * AND LOAD ACCA WITH SUB TOKEN ($A6)
*
* DATA
DATA      BSR  LAEE8          MOVE INPUT POINTER TO END OF SUBLINE OR LINE
          FCB  SKP2           SKIP 2 BYTES

* REM, ELSE
ELSE
REM       BSR  LAEEB          MOVE INPUT POINTER TO END OF LINE
          STX  CHARAD         RESET BASIC'S INPUT POINTER
LAEE7     RTS
* ADVANCE INPUT POINTER TO END OF SUBLINE OR LINE
LAEE8     LDB  #':            COLON = SUBLINE TERMINATOR CHARACTER
LAEEA     FCB  SKP1LD         SKPILD SKIP ONE BYTE; LDA #$5F
* ADVANCE BASIC'S INPUT POINTER TO END OF
* LINE - RETURN ADDRESS OF END OF LINE+1 IN X
LAEEB     CLRB                0 = LINE TERMINATOR CHARACTER
          STB  CHARAC         TEMP STORE PRIMARY TERMINATOR CHARACTER
          CLRB                0 (END OF LINE) = ALTERNATE TERM. CHAR.
          LDX  CHARAD         LOAD X W/BASIC'S INPUT POINTER
LAEF1     TFR  B,A            * CHANGE TERMINATOR CHARACTER
          LDB  CHARAC         * FROM ACCB TO CHARAC - SAVE OLD TERMINATOR
*         IN   CHARAC
          STA  CHARAC         SWAP PRIMARY AND SECONDARY TERMINATORS
LAEF7     LDA  ,X             GET NEXT INPUT CHARACTER
          BEQ  LAEE7          RETURN IF 0 (END OF LINE)
          PSHS B              SAVE TERMINATOR ON STACK
          CMPA ,S+            COMPARE TO INPUT CHARACTER
          BEQ  LAEE7          RETURN IF EQUAL
          LEAX 1,X            MOVE POINTER UP ONE
          CMPA #'"            CHECK FOR DOUBLE QUOTES
          BEQ  LAEF1          BRANCH IF " - TOGGLE TERMINATOR CHARACTERS
          INCA                * CHECK FOR $FF AND BRANCH IF
          BNE  LAF0C          * NOT SECONDARY TOKEN
          LEAX 1,X            MOVE INPUT POINTER 1 MORE IF SECONDARY
LAF0C     CMPA #TOK_IF+1      TOKEN FOR IF?
          BNE  LAEF7          NO - GET ANOTHER INPUT CHARACTER
          INC  IFCTR          INCREMENT IF COUNTER - KEEP TRACK OF HOW MANY
*                             'IF' STATEMENTS ARE NESTED IN ONE LINE
          BRA  LAEF7          GET ANOTHER INPUT CHARACTER

* IF
IF        JSR  LB141          EVALUATE NUMERIC EXPRESSION
          JSR  GETCCH         GET CURRENT INPUT CHARACTER
          CMPA #TOK_GO        TOKEN FOR GO
          BEQ  LAF22          TREAT 'GO' THE SAME AS 'THEN'
          LDB  #TOK_THEN      TOKEN FOR THEN
          JSR  LB26F          DO A SYNTAX CHECK ON ACCB
LAF22     LDA  FP0EXP         CHECK FOR TRUE/FALSE - FALSE IF FPA0 EXPONENT = ZERO
          BNE  LAF39          BRANCH IF CONDITION TRUE
          CLR  IFCTR          CLEAR FLAG - KEEP TRACK OF WHICH NESTED ELSE STATEMENT
*                             TO SEARCH FOR IN NESTED 'IF' LOOPS
LAF28     BSR  DATA           MOVE BASIC'S POINTER TO END OF SUBLINE
          TSTA                * CHECK TO SEE IF END OF LINE OR SUBLINE
          BEQ  LAEE7          * AND RETURN IF END OF LINE
          JSR  GETNCH         GET AN INPUT CHARACTER FROM BASIC
          CMPA #TOK_ELSE      TOKEN FOR ELSE
          BNE  LAF28          IGNORE ALL DATA EXCEPT 'ELSE' UNTIL
*                             END OF LINE (ZERO BYTE)
          DEC  IFCTR          CHECK TO SEE IF YOU MUST SEARCH ANOTHER SUBLINE
          BPL  LAF28          BRANCH TO SEARCH ANOTHER SUBLINE FOR 'ELSE'
          JSR  GETNCH         GET AN INPUT CHARACTER FROM BASIC
LAF39     JSR  GETCCH         GET CURRENT INPUT CHARACTER
          LBCS LAEA4          BRANCH TO 'GOTO' IF NUMERIC CHARACTER
          JMP  LADC6          RETURN TO MAIN INTERPRETATION LOOP

* ON
ON        JSR  LB70B          EVALUATE EXPRESSION
          LDB  #TOK_GO        TOKEN FOR GO
          JSR  LB26F          SYNTAX CHECK FOR GO
          PSHS A              SAVE NEW TOKEN (TO,SUB)
          CMPA #TOK_SUB       TOKEN FOR SUB?
          BEQ  LAF54          YES
          CMPA #TOK_TO        TOKEN FOR TO?
LAF52     BNE  LAED7          'SYNTAX' ERROR IF NOT 'SUB' OR 'TO'
LAF54     DEC  FPA0+3         DECREMENT IS BYTE OF MANTISSA OF FPA0 - THIS
*                             IS THE ARGUMENT OF THE 'ON' STATEMENT
          BNE  LAF5D          BRANCH IF NOT AT THE PROPER GOTO OR GOSUB LINE NUMBER
          PULS B              GET BACK THE TOKEN FOLLOWING 'GO'
          JMP  LAE88          GO DO A 'GOTO' OR 'GOSUB'
LAF5D     JSR  GETNCH         GET A CHARACTER FROM BASIC
          BSR  LAF67          CONVERT BASIC LINE NUMBER TO BINARY
          CMPA #',            IS CHARACTER FOLLOWING LINE NUMBER A COMMA?
          BEQ  LAF54          YES
          PULS B,PC           IF NOT, FALL THROUGH TO NEXT COMMAND
LAF67     LDX  ZERO           DEFAULT LINE NUMBER OF ZERO
          STX  BINVAL         SAVE IT IN BINVAL
*
* CONVERT LINE NUMBER TO BINARY - RETURN VALUE IN BINVAL
*
LAF6B     BCC  LAFCE          RETURN IF NOT NUMERIC CHARACTER
          SUBA #'0            MASK OFF ASCII
          STA  CHARAC         SAVE DIGIT IN VO1
          LDD  BINVAL         GET ACCUMULATED LINE NUMBER VALUE
          CMPA #24            LARGEST LINE NUMBER IS $F9FF (63999) -
*         (24*256+255)*10+9
          BHI  LAF52          'SYNTAX' ERROR IF TOO BIG
* MULT ACCD X 10
          ASLB                *
          ROLA                * TIMES 2
          ASLB                =
          ROLA                = TIMES 4
          ADDD BINVAL         ADD 1 = TIMES 5
          ASLB                *
          ROLA                * TIMES 10
          ADDB CHARAC         ADD NEXT DIGIT
          ADCA #0             PROPAGATE CARRY
          STD  BINVAL         SAVE NEW ACCUMULATED LINE NUMBER
          JSR  GETNCH         GET NEXT CHARACTER FROM BASIC
          BRA  LAF6B          LOOP- PROCESS NEXT DIGIT
*
* LET (EXBAS)
* EVALUATE A NON-TOKEN EXPRESSION
* TARGET = REPLACEMENT
LET       JSR  LB357          FIND TARGET VARIABLE DESCRIPTOR
          STX  VARDES         SAVE DESCRIPTOR ADDRESS OF 1ST EXPRESSION
          LDB  #TOK_EQUALS    TOKEN FOR "="
          JSR  LB26F          DO A SYNTAX CHECK FOR '='
          LDA  VALTYP         * GET VARIABLE TYPE AND
          PSHS A              * SAVE ON THE STACK
          JSR  LB156          EVALUATE EXPRESSION
          PULS A              * REGET VARIABLE TYPE OF 1ST EXPRESSION AND
          RORA                * SET CARRY IF STRING
          JSR  LB148          TYPE CHECK-TM ERROR IF VARIABLE TYPES ON
*                             BOTH SIDES OF EQUALS SIGN NOT THE SAME
          LBEQ LBC33          GO PUT FPA0 INTO VARIABLE DESCRIPTOR IF NUMERIC
* MOVE A STRING WHOSE DESCRIPTOR IS LOCATED AT
* FPA0+2 INTO THE STRING SPACE. TRANSFER THE
* DESCRIPTOR ADDRESS TO THE ADDRESS IN VARDES
* DON’T MOVE THE STRING IF IT IS ALREADY IN THE
* STRING SPACE. REMOVE DESCRIPTOR FROM STRING
* STACK IF IT IS LAST ONE ON THE STACK
LAFA4     LDX  FPA0+2         POINT X TO DESCRIPTOR OF REPLACEMENT STRING
          LDD  FRETOP         LOAD ACCD WITH START OF STRING SPACE
          CMPD 2,X            IS THE STRING IN STRING SPACE?
          BCC  LAFBE          BRANCH IF IT'S NOT IN THE STRING SPACE
          CMPX VARTAB         COMPARE DESCRIPTOR ADDRESS TO START OF VARIABLES
          BCS  LAFBE          BRANCH IF DESCRIPTOR ADDRESS NOT IN VARIABLES
LAFB1     LDB  ,X             GET LENGTH OF REPLACEMENT STRING
          JSR  LB50D          RESERVE ACCB BYTES OF STRING SPACE
          LDX  V4D            GET DESCRIPTOR ADDRESS BACK
          JSR  LB643          MOVE STRING INTO STRING SPACE
          LDX  #STRDES        POINT X TO TEMP STRING DESCRIPTOR ADDRESS
LAFBE     STX  V4D            SAVE STRING DESCRIPTOR ADDRESS IN V4D
          JSR  LB675          REMOVE STRING DESCRIPTOR IF LAST ONE
*              ON STRING STACK
          LDU  V4D            POINT U TO REPLACEMENT DESCRIPTOR ADDRESS
          LDX  VARDES         GET TARGET DESCRIPTOR ADDRESS
          PULU A,B,Y          GET LENGTH AND START OF REPLACEMENT STRING
          STA  ,X             * SAVE STRING LENGTH AND START IN
          STY  2,X            * TARGET DESCRIPTOR LOCATION
LAFCE     RTS

LAFCF     FCC  "?REDO"        ?REDO MESSAGE
          FCB  CR,$00

LAFD6
LAFDC     JMP  LAC46          JMP TO ERROR HANDLER
LAFDF     LDA  INPFLG         = GET THE INPUT FLAG AND BRANCH
          BEQ  LAFEA          = IF 'INPUT'
          LDX  DATTXT         * GET LINE NUMBER WHERE THE ERROR OCCURRED
          STX  CURLIN         * AND USE IT AS THE CURRENT LINE NUMBER
          JMP  LB277          'SYNTAX ERROR'
LAFEA     LDX  #LAFCF-1       * POINT X TO '?REDO' AND PRINT
          JSR  LB99C          * IT ON THE SCREEN
          LDX  TINPTR         = GET THE SAVED ABSOLUTE ADDRESS OF
          STX  CHARAD         = INPUT POINTER AND RESTORE IT
          RTS
*
* INPUT
INPUT     LDB  #11*2          'ID' ERROR
          LDX  CURLIN         GET CURRENT LINE NUMBER
          LEAX 1,X            ADD ONE
          BEQ  LAFDC          'ID' ERROR BRANCH IF DIRECT MODE
          BSR  LB00F          GET SOME INPUT DATA - WAS LB002
          RTS
LB00F     CMPA #'"            CHECK FOR PROMPT STRING DELIMITER: "
          BNE  LB01E          BRANCH IF NO PROMPT STRING
          JSR  LB244          PUT PROMPT STRING ON STRING STACK
          LDB  #';            *
          JSR  LB26F          * DO A SYNTAX CHECK FOR SEMICOLON
          JSR  LB99F          PRINT MESSAGE TO CONSOLE OUT
LB01E     LDX  #LINBUF        POINT TO BASIC'S LINE BUFFER
          CLR  ,X             CLEAR 1ST BYTE - FLAG TO INDICATE NO DATA
*                             IN LINE BUFFER
          BSR  LB02F          INPUT A STRING TO LINE BUFFER
          LDB  #',            * INSERT A COMMA AT THE END
          STB  ,X             * OF THE LINE INPUT BUFFER
          BRA  LB049
* FILL BASIC'S LINE INPUT BUFFER CONSOLE IN
LB02F     JSR  LB9AF          SEND A "?" TO CONSOLE OUT
          JSR  LB9AC          SEND A 'SPACE' TO CONSOLE OUT
LB035     JSR  LA390          GO READ IN A BASIC LINE
          BCC  LB03F          BRANCH IF ENTER KEY ENDED ENTRY
          LEAS 4,S            PURGE TWO RETURN ADDRESSES OFF THE STACK
          JMP  LAE11          GO DO A 'STOP' IF BREAK KEY ENDED LINE ENTRY
LB03F     LDB  #2*23          'INPUT PAST END OF FILE' ERROR
          RTS
*
* READ
READ      LDX  DATPTR         GET 'READ' START ADDRESS
          FCB  SKP1LD         SKIP ONE BYTE - LDA #*$4F
LB049     CLRA                'INPUT' ENTRY POINT: INPUT FLAG = 0
          STA  INPFLG         SET INPUT FLAG; 0 = INPUT: <> 0 = READ
          STX  DATTMP         SAVE 'READ' START ADDRESS/'INPUT' BUFFER START
LB04E     JSR  LB357          EVALUATE A VARIABLE
          STX  VARDES         SAVE DESCRIPTOR ADDRESS
          LDX  CHARAD         * GET BASIC'S INPUT POINTER
          STX  BINVAL         * AND SAVE IT
          LDX  DATTMP         GET 'READ' ADDRESS START/'INPUT' BUFFER POINTER
          LDA  ,X             GET A CHARACTER FROM THE BASIC PROGRAM
          BNE  LB069          BRANCH IF NOT END OF LINE
          LDA  INPFLG         * CHECK INPUT FLAG AND BRANCH
          BNE  LB0B9          * IF LOOKING FOR DATA (READ)
* NO DATA IN 'INPUT' LINE BUFFER AND/OR INPUT
* NOT COMING FROM SCREEN
          JSR  LB9AF          SEND A '?' TO CONSOLE OUT
          BSR  LB02F          FILL INPUT BUFFER FROM CONSOLE IN
LB069     STX  CHARAD         RESET BASIC'S INPUT POINTER
          JSR  GETNCH         GET A CHARACTER FROM BASIC
          LDB  VALTYP         * CHECK VARIABLE TYPE AND
          BEQ  LB098          * BRANCH IF NUMERIC
* READ/INPUT A STRING VARIABLE
          LDX  CHARAD         LOAD X WITH CURRENT BASIC INPUT POINTER
          STA  CHARAC         SAVE CURRENT INPUT CHARACTER
          CMPA #'"            CHECK FOR STRING DELIMITER: "
          BEQ  LB08B          BRANCH IF STRING DELIMITER
          LEAX -1,X           BACK UP POINTER
          CLRA                * ZERO = END OF LINE CHARACTER
          STA  CHARAC         * SAVE AS TERMINATOR
          JSR  LA35F          SET UP PRINT PARAMETERS
          LDA  #':            END OF SUBLINE CHARACTER
          STA  CHARAC         SAVE AS TERMINATOR I
          LDA  #',            COMMA
LB08B     STA  ENDCHR         SAVE AS TERMINATOR 2
          JSR  LB51E          STRIP A STRING FROM THE INPUT BUFFER
          JSR  LB249          MOVE INPUT POINTER TO END OF STRING
          JSR  LAFA4          PUT A STRING INTO THE STRING SPACE IF NECESSARY
          BRA  LB09E          CHECK FOR ANOTHER DATA ITEM
* SAVE A NUMERIC VALUE IN A READ OR INPUT DATA ITEM
LB098     JSR  LBD12          CONVERT AN ASCII STRING TO FP NUMBER
          JSR  LBC33          PACK FPA0 AND STORE IT IN ADDRESS IN VARDES -
*                             INPUT OR READ DATA ITEM
LB09E     JSR  GETCCH         GET CURRENT INPUT CHARACTER
          BEQ  LB0A8          BRANCH IF END OF LINE
          CMPA #',            CHECK FOR A COMMA
          LBNE LAFD6          BAD FILE DATA' ERROR OR RETRY
LB0A8     LDX  CHARAD         * GET CURRENT INPUT
          STX  DATTMP         * POINTER (USED AS A DATA POINTER) AND SAVE IT
          LDX  BINVAL         * RESET INPUT POINTER TO INPUT OR
          STX  CHARAD         * READ STATEMENT
          JSR  GETCCH         GET CURRENT CHARACTER FROM BASIC
          BEQ  LB0D5          BRANCH IF END OF LINE - EXIT COMMAND
          JSR  LB26D          SYNTAX CHECK FOR COMMA
          BRA  LB04E          GET ANOTHER INPUT OR READ ITEM
* SEARCH FROM ADDRESS IN X FOR
* 1ST OCCURENCE OF THE TOKEN FOR DATA
LB0B9     STX  CHARAD         RESET BASIC'S INPUT POINTER
          JSR  LAEE8          SEARCH FOR END OF CURRENT LINE OR SUBLINE
          LEAX 1,X            MOVE X ONE PAST END OF LINE
          TSTA                CHECK FOR END OF LINE
          BNE  LB0CD          BRANCH IF END OF SUBLINE
          LDB  #2*3           'OUT OF DATA' ERROR
          LDU  ,X++           GET NEXT 2 CHARACTERS
          BEQ  LB10A          'OD' ERROR IF END OF PROGRAM
          LDD  ,X++           GET BASIC LINE NUMBER AND
          STD  DATTXT         SAVE IT IN DATTXT
LB0CD     LDA  ,X             GET AN INPUT CHARACTER
          CMPA #TOK_DATA      DATA TOKEN?
          BNE  LB0B9          NO - KEEP LOOKING
          BRA  LB069          YES
* EXIT READ AND INPUT COMMANDS
LB0D5     LDX  DATTMP         GET DATA POINTER
          LDB  INPFLG         * CHECK INPUT FLAG
          LBNE LADE8          * SAVE NEW DATA POINTER IF READ
          LDA  ,X             = CHECK NEXT CHARACTER IN 'INPUT' BUFFER
          BEQ  LB0E7          =
          LDX  #LB0E8-1       POINT X TO '?EXTRA IGNORED'
          JMP  LB99C          PRINT THE MESSAGE
LB0E7     RTS

LB0E8     FCC  "?EXTRA IGNORED" ?EXTRA IGNORED MESSAGE


          FCB  CR,$00

* NEXT
NEXT      BNE  LB0FE          BRANCH IF ARGUMENT GIVEN
          LDX  ZERO           X = 0: DEFAULT FOR NO ARGUMENT
          BRA  LB101
LB0FE     JSR  LB357          EVALUATE AN ALPHA EXPRESSION
LB101     STX  VARDES         SAVE VARIABLE DESCRIPTOR POINTER
          JSR  LABF9          GO SCAN FOR 'FOR/NEXT' DATA ON STACK
          BEQ  LB10C          BRANCH IF DATA FOUND
          LDB  #0             'NEXT WITHOUT FOR' ERROR (SHOULD BE CLRB)
LB10A     BRA  LB153          PROCESS ERROR
LB10C     TFR  X,S            POINT S TO START OF 'FOR/NEXT' DATA
          LEAX 3,X            POINT X TO FP VALUE OF STEP
          JSR  LBC14          COPY A FP NUMBER FROM (X) TO FPA0
          LDA  8,S            GET THE DIRECTION OF STEP
          STA  FP0SGN         SAVE IT AS THE SIGN OF FPA0
          LDX  VARDES         POINT (X) TO INDEX VARIABLE DESCRIPTOR
          JSR  LB9C2          ADD (X) TO FPA0 (STEP TO INDEX)
          JSR  LBC33          PACK FPA0 AND STORE IT IN ADDRESS
*                             CONTAINED IN VARDES
          LEAX 9,S            POINT (X) TO TERMINAL VALUE OF INDEX
          JSR  LBC96          COMPARE CURRENT INDEX VALUE TO TERMINAL VALUE OF INDEX
          SUBB 8,S            ACCB = 0 IF TERMINAL VALUE=CURRENT VALUE AND STEP=0 OR IF
*                             STEP IS POSITIVE AND CURRENT VALUE>TERMINAL VALUE OR
*                             STEP IS NEGATIVE AND CURRENT VALUE<TERMINAL VALUE
          BEQ  LB134          BRANCH IF 'FOR/NEXT' LOOP DONE
          LDX  14,S           * GET LINE NUMBER AND
          STX  CURLIN         * BASIC POINTER OF
          LDX  16,S           * STATEMENT FOLLOWING THE
          STX  CHARAD         * PROPER FOR STATEMENT
LB131     JMP  LAD9E          JUMP BACK TO COMMAND INTEPR. LOOP
LB134     LEAS 18,S           PULL THE 'FOR-NEXT' DATA OFF THE STACK
          JSR  GETCCH         GET CURRENT INPUT CHARACTER
          CMPA #',            CHECK FOR ANOTHER ARGUMENT
          BNE  LB131          RETURN IF NONE
          JSR  GETNCH         GET NEXT CHARACTER FROM BASIC
          BSR  LB0FE          BSR SIMULATES A CALL TO 'NEXT' FROM COMMAND LOOP


LB141     BSR  LB156          EVALUATE EXPRESSION AND DO A TYPE CHECK FOR NUMERIC
LB143     ANDCC #$FE          CLEAR CARRY FLAG
LB145     FCB  $7D            OP CODE OF TST $1A01 - SKIP TWO BYTES (DO
*              NOT CHANGE CARRY FLAG)
LB146     ORCC #1             SET CARRY

* STRING TYPE MODE CHECK - IF ENTERED AT LB146 THEN VALTYP PLUS IS 'TM' ERROR
* NUMERIC TYPE MODE CHECK - IF ENTERED AT LB143 THEN VALTYP MINUS IS 'TM' ERROR
* IF ENTERED AT LB148, A TYPE CHECK IS DONE ON VALTYP
* IF ENTERED WITH CARRY SET, THEN 'TM' ERROR IF NUMERIC
* IF ENTERED WITH CARRY CLEAR, THEN 'TM' ERROR IF STRING.
LB148     TST  VALTYP         TEST TYPE FLAG; DO NOT CHANGE CARRY
          BCS  LB14F          BRANCH IF STRING
          BPL  LB0E7          RETURN ON PLUS
          FCB  SKP2           SKIP 2 BYTES - 'TM' ERROR
LB14F     BMI  LB0E7          RETURN ON MINUS
          LDB  #12*2          'TYPE M1SMATCH' ERROR
LB153     JMP  LAC46          PROCESS ERROR
* EVALUATE EXPRESSION
LB156     BSR  LB1C6          BACK UP INPUT POINTER
LB158     CLRA                END OF OPERATION PRECEDENCE FLAG
          FCB  SKP2           SKIP TWO BYTES
LB15A     PSHS B              SAVE FLAG (RELATIONAL OPERATOR FLAG)
          PSHS A              SAVE FLAG (PRECEDENCE FLAG)
          LDB  #1             *
          JSR  LAC33          * SEE IF ROOM IN FREE RAM FOR (B) WORDS
          JSR  LB223          GO EVALUATE AN EXPRESSION
          CLR  TRELFL         RESET RELATIONAL OPERATOR FLAG
LB168     JSR  GETCCH         GET CURRENT INPUT CHARACTER
* CHECK FOR RELATIONAL OPERATORS
LB16A     SUBA #TOK_GREATER   TOKEN FOR >
          BCS  LB181          BRANCH IF LESS THAN RELATIONAL OPERATORS
          CMPA #3             *
          BCC  LB181          * BRANCH IF GREATER THAN RELATIONAL OPERATORS
          CMPA #1             SET CARRY IF '>'
          ROLA                CARRY TO BIT 0
          EORA TRELFL         * CARRY SET IF
          CMPA TRELFL         * TRELFL = ACCA
          BCS  LB1DF          BRANCH IF SYNTAX ERROR : == << OR >>
          STA  TRELFL         BIT 0: >, BIT 1 =, BIT 2: <
          JSR  GETNCH         GET AN INPUT CHARACTER
          BRA  LB16A          CHECK FOR ANOTHER RELATIONAL OPERATOR
*
LB181     LDB  TRELFL         GET RELATIONAL OPERATOR FLAG
          BNE  LB1B8          BRANCH IF RELATIONAL COMPARISON
          LBCC LB1F4          BRANCH IF > RELATIONAL OPERATOR
          ADDA #7             SEVEN ARITHMETIC/LOGICAL OPERATORS
          BCC  LB1F4          BRANCH IF NOT ARITHMETIC/LOGICAL OPERATOR
          ADCA VALTYP         ADD CARRY, NUMERIC FLAG AND MODIFIED TOKEN NUMBER
          LBEQ LB60F          BRANCH IF VALTYP = FF, AND ACCA = '+' TOKEN -
*                             CONCATENATE TWO STRINGS
          ADCA #-1            RESTORE ARITHMETIC/LOGICAL OPERATOR NUMBER
          PSHS A              * STORE OPERATOR NUMBER ON STACK; MULTIPLY IT BY 2
          ASLA                * THEN ADD THE STORED STACK DATA = MULTIPLY
          ADDA ,S+            * X 3; 3 BYTE/TABLE ENTRY
          LDX  #LAA51         JUMP TABLE FOR ARITHMETIC & LOGICAL OPERATORS
          LEAX A,X            POINT X TO PROPER TABLE
LB19F     PULS A              GET PRECEDENCE FLAG FROM STACK
          CMPA ,X             COMPARE TO CURRENT OPERATOR
          BCC  LB1FA          BRANCH IF STACK OPERATOR > CURRENT OPERATOR
          BSR  LB143          'TM' ERROR IF VARIABLE TYPE = STRING

* OPERATION BEING PROCESSED IS OF HIGHER PRECEDENCE THAN THE PREVIOUS OPERATION.
LB1A7     PSHS A              SAVE PRECEDENCE FLAG
          BSR  LB1D4          PUSH OPERATOR ROUTINE ADDRESS AND FPA0 ONTO STACK
          LDX  RELPTR         GET POINTER TO ARITHMETIC/LOGICAL TABLE ENTRY FOR
*                             LAST CALCULATED OPERATION
          PULS A              GET PRECEDENCE FLAG OF PREVIOUS OPERATION
          BNE  LB1CE          BRANCH IF NOT END OF OPERATION
          TSTA                CHECK TYPE OF PRECEDENCE FLAG
          LBEQ LB220          BRANCH IF END OF EXPRESSION OR SUB-EXPRESSION
          BRA  LB203          EVALUATE AN OPERATION

LB1B8     ASL  VALTYP         BIT 7 OF TYPE FLAG TO CARRY
          ROLB                SHIFT RELATIONAL FLAG LEFT - VALTYP TO BIT 0
          BSR  LB1C6          MOVE THE INPUT POINTER BACK ONE
          LDX  #LB1CB         POINT X TO RELATIONAL COMPARISON JUMP TABLE
          STB  TRELFL         SAVE RELATIONAL COMPARISON DATA
          CLR  VALTYP         SET VARIABLE TYPE TO NUMERIC
          BRA  LB19F          PERFORM OPERATION OR SAVE ON STACK

LB1C6     LDX  CHARAD         * GET BASIC'S INPUT POINTER AND
          JMP  LAEBB          * MOVE IT BACK ONE
* RELATIONAL COMPARISON JUMP TABLE
LB1CB     FCB  $64            RELATIONAL COMPARISON FLAG
LB1CC     FDB  LB2F4          JUMP ADDRESS

LB1CE     CMPA ,X             COMPARE PRECEDENCE OF LAST DONE OPERATION TO
*         NEXT TO BE DONE OPERATION
          BCC  LB203          EVALUATE OPERATION IF LOWER PRECEDENCE
          BRA  LB1A7          PUSH OPERATION DATA ON STACK IF HIGHER PRECEDENCE

* PUSH OPERATOR EVALUATION ADDRESS AND FPA0 ONTO STACK AND EVALUATE ANOTHER EXPR
LB1D4     LDD  1,X            GET ADDRESS OF OPERATOR ROUTINE
          PSHS B,A            SAVE IT ON THE STACK
          BSR  LB1E2          PUSH FPA0 ONTO STACK
          LDB  TRELFL         GET BACK RELATIONAL OPERATOR FLAG
          LBRA LB15A          EVALUATE ANOTHER EXPRESSION
LB1DF     JMP  LB277          'SYNTAX ERROR'
* PUSH FPA0 ONTO THE STACK. ,S   = EXPONENT
* 1-2,S =HIGH ORDER MANTISSA 3-4,S = LOW ORDER MANTISSA
* 5,S = SIGN RETURN WITH PRECEDENCE CODE IN ACCA
LB1E2     LDB  FP0SGN         GET SIGN OF FPA0 MANTISSA
          LDA  ,X             GET PRECEDENCE CODE TO ACCA
LB1E6     PULS Y              GET RETURN ADDRESS FROM STACK & PUT IT IN Y
          PSHS B              SAVE ACCB ON STACK
LB1EA     LDB  FP0EXP         * PUSH FPA0 ONTO THE STACK
          LDX  FPA0           *
          LDU  FPA0+2         *
          PSHS U,X,B          *
          JMP  ,Y             JUMP TO ADDRESS IN Y

* BRANCH HERE IF NON-OPERATOR CHARACTER FOUND - USUALLY ')' OR END OF LINE
LB1F4     LDX  ZERO           POINT X TO DUMMY VALUE (ZERO)
          LDA  ,S+            GET PRECEDENCE FLAG FROM STACK
          BEQ  LB220          BRANCH IF END OF EXPRESSION
LB1FA     CMPA #$64           * CHECK FOR RELATIONAL COMPARISON FLAG
          BEQ  LB201          * AND BRANCH IF RELATIONAL COMPARISON
          JSR  LB143          'TM' ERROR IF VARIABLE TYPE = STRING
LB201     STX  RELPTR         SAVE POINTER TO OPERATOR ROUTINE
LB203     PULS B              GET RELATIONAL OPERATOR FLAG FROM STACK
          CMPA #$5A           CHECK FOR 'NOT' OPERATOR
          BEQ  LB222          RETURN IF 'NOT' - NO RELATIONAL COMPARISON
          CMPA #$7D           CHECK FOR NEGATION (UNARY) FLAG
          BEQ  LB222          RETURN IF NEGATION - NO RELATIONAL COMPARISON

* EVALUATE AN OPERATION. EIGHT BYTES WILL BE STORED ON STACK, FIRST SIX BYTES
* ARE A TEMPORARY FLOATING POINT RESULT THEN THE ADDRESS OF ROUTINE WHICH
* WILL EVALUATE THE OPERATION. THE RTS AT END OF ROUTINE WILL VECTOR
* TO EVALUATING ROUTINE.
          LSRB                = ROTATE VALTYP BIT INTO CARRY
          STB  RELFLG         = FLAG AND SAVE NEW RELFLG
          PULS A,X,U          * PULL A FP VALUE OFF OF THE STACK
          STA  FP1EXP         * AND SAVE IT IN FPA1
          STX  FPA1           *
          STU  FPA1+2         *
          PULS B              = GET MANTISSA SIGN AND
          STB  FP1SGN         = SAVE IT IN FPA1
          EORB FP0SGN         EOR IT WITH FPA1 MANTISSA SIGN
          STB  RESSGN         SAVE IT IN RESULT SIGN BYTE
LB220     LDB  FP0EXP         GET EXPONENT OF FPA0
LB222     RTS

LB223     JSR  XVEC15         CALL EXTENDED BASIC ADD-IN
          CLR  VALTYP         INITIALIZE TYPE FLAG TO NUMERIC
          JSR  GETNCH         GET AN INPUT CHAR
          BCC  LB22F          BRANCH IF NOT NUMERIC
LB22C     JMP  LBD12          CONVERT ASCII STRING TO FLOATING POINT -
*         RETURN RESULT IN FPA0
* PROCESS A NON NUMERIC FIRST CHARACTER
LB22F     JSR  LB3A2          SET CARRY IF NOT ALPHA
          BCC  LB284          BRANCH IF ALPHA CHARACTER
          CMPA #'.            IS IT '.' (DECIMAL POINT)?
          BEQ  LB22C          CONVERT ASCII STRING TO FLOATING POINT
          CMPA #TOK_MINUS     MINUS TOKEN
          BEQ  LB27C          YES - GO PROCESS THE MINUS OPERATOR
          CMPA #TOK_PLUS      PLUS TOKEN
          BEQ  LB223          YES - GET ANOTHER CHARACTER
          CMPA #'"            STRING DELIMITER: " ?
          BNE  LB24E          NO
LB244     LDX  CHARAD         CURRENT BASIC POINTER TO X
          JSR  LB518          SAVE STRING ON STRING STACK
LB249     LDX  COEFPT         * GET ADDRESS OF END OF STRING AND
          STX  CHARAD         * PUT BASIC'S INPUT POINTER THERE
          RTS
LB24E     CMPA #TOK_NOT       NOT TOKEN?
          BNE  LB25F          NO
* PROCESS THE NOT OPERATOR
          LDA  #$5A           'NOT' PRECEDENCE FLAG
          JSR  LB15A          PROCESS OPERATION FOLLOWING 'NOT'
          JSR  INTCNV         CONVERT FPA0 TO INTEGER IN ACCD
          COMA                * 'NOT' THE INTEGER
          COMB                *
          JMP  GIVABF         CONVERT ACCD TO FLOATING POINT (FPA0)
LB25F     INCA                CHECK FOR TOKENS PRECEEDED BY $FF
          BEQ  LB290          IT WAS PRECEEDED BY $FF
LB262     BSR  LB26A          SYNTAX CHECK FOR A '('
          JSR  LB156          EVALUATE EXPRESSIONS WITHIN PARENTHESES AT
*         HIGHEST PRECEDENCE
LB267     LDB  #')            SYNTAX CHECK FOR ')'
          FCB  SKP2           SKIP 2 BYTES
LB26A     LDB  #'(            SYNTAX CHECK FOR '('
          FCB  SKP2           SKIP 2 BYTES
LB26D     LDB  #',            SYNTAX CHECK FOR COMMA
LB26F     CMPB [CHARAD]       * COMPARE ACCB TO CURRENT INPUT
          BNE  LB277          * CHARACTER - SYNTAX ERROR IF NO MATCH
          JMP  GETNCH         GET A CHARACTER FROM BASIC
LB277     LDB  #2*1           SYNTAX ERROR
          JMP  LAC46          JUMP TO ERROR HANDLER

* PROCESS THE MINUS (UNARY) OPERATOR
LB27C     LDA  #$7D           MINUS (UNARY) PRECEDENCE FLAG
          JSR  LB15A          PROCESS OPERATION FOLLOWING 'UNARY' NEGATION
          JMP  LBEE9          CHANGE SIGN OF FPA0 MANTISSA

* EVALUATE ALPHA EXPRESSION
LB284     JSR  LB357          FIND THE DESCRIPTOR ADDRESS OF A VARIABLE
LB287     STX  FPA0+2         SAVE DESCRIPTOR ADDRESS IN FPA0
          LDA  VALTYP         TEST VARIABLE TYPE
          BNE  LB222          RETURN IF STRING
          JMP  LBC14          COPY A FP NUMBER FROM (X) TO FPA0

* EVALUATING A SECONDARY TOKEN
LB290     JSR  GETNCH         GET AN INPUT CHARACTER (SECONDARY TOKEN)
          TFR  A,B            SAVE IT IN ACCB
          ASLB                X2 & BET RID OF BIT 7
          JSR  GETNCH         GET ANOTHER INPUT CHARACTER
          CMPB #NUM_SEC_FNS-1*2 29 SECONDARY FUNCTIONS - 1
          BLS  LB29F          BRANCH IF COLOR BASIC TOKEN
          JMP  LB277          SYNTAX ERROR
LB29F     PSHS B              SAVE TOKEN OFFSET ON STACK
          CMPB #TOK_LEFT-$80*2 CHECK FOR TOKEN WITH AN ARGUMENT
          BCS  LB2C7          DO SECONDARIES STRING$ OR LESS
          CMPB #TOK_INKEY-$80*2 *
          BCC  LB2C9          * DO SECONDARIES $92 (INKEY$) OR >
          BSR  LB26A          SYNTAX CHECK FOR A '('
          LDA  ,S             GET TOKEN NUMBER
* DO SECONDARIES (LEFT$, RIGHT$, MID$)
          JSR  LB156          EVALUATE FIRST STRING IN ARGUMENT
          BSR  LB26D          SYNTAX CHECK FOR A COMMA
          JSR  LB146          'TM' ERROR IF NUMERIC VARIABLE
          PULS A              GET TOKEN OFFSET FROM STACK
          LDU  FPA0+2         POINT U TO STRING DESCRIPTOR
          PSHS U,A            SAVE TOKEN OFFSET AND DESCRIPTOR ADDRESS
          JSR  LB70B          EVALUATE FIRST NUMERIC ARGUMENT
          PULS A              GET TOKEN OFFSET FROM STACK
          PSHS B,A            SAVE TOKEN OFFSET AND NUMERIC ARGUMENT
          FCB  $8E            OP CODE OF LDX# - SKIP 2 BYTES
LB2C7     BSR  LB262          SYNTAX CHECK FOR A '('
LB2C9     PULS B              GET TOKEN OFFSET
          LDX  COMVEC+8       GET SECONDARY FUNCTION JUMP TABLE ADDRESS
LB2CE     ABX                 ADD IN COMMAND OFFSET
*
* HERE IS WHERE WE BRANCH TO A SECONDARY FUNCTION
          JSR  [,X]           GO DO AN SECONDARY FUNCTION
          JMP  LB143          'TM' ERROR IF VARIABLE TYPE = STRING

* LOGICAL OPERATOR 'OR' JUMPS HERE
LB2D4     FCB  SKP1LD         SKIP ONE BYTE - 'OR' FLAG = $4F

* LOGICAL OPERATOR 'AND' JUMPS HERE
LB2D5     CLRA                AND FLAG = 0
          STA  TMPLOC         AND/OR FLAG
          JSR  INTCNV         CONVERT FPA0 INTO AN INTEGER IN ACCD
          STD  CHARAC         TEMP SAVE ACCD
          JSR  LBC4A          MOVE FPA1 TO FPA0
          JSR  INTCNV         CONVERT FPA0 INTO AN INTEGER IN ACCD
          TST  TMPLOC         CHECK AND/OR FLAG
          BNE  LB2ED          BRANCH IF OR
          ANDA CHARAC         * 'AND' ACCD WITH FPA0 INTEGER
          ANDB ENDCHR         * STORED IN ENDCHR
          BRA  LB2F1          CONVERT TO FP
LB2ED     ORA  CHARAC         * 'OR' ACCD WITH FPA0 INTEGER
          ORB  ENDCHR         * STORED IN CHARAC
LB2F1     JMP  GIVABF         CONVERT THE VALUE IN ACCD INTO A FP NUMBER

* RELATIONAL COMPARISON PROCESS HANDLER
LB2F4     JSR  LB148          'TM' ERROR IF TYPE MISMATCH
          BNE  LB309          BRANCH IF STRING VARIABLE
          LDA  FP1SGN         * 'PACK' THE MANTISSA
          ORA  #$7F           * SIGN OF FPA1 INTO
          ANDA FPA1           * BIT 7 OF THE
          STA  FPA1           * MANTISSA MS BYTE
          LDX  #FP1EXP        POINT X TO FPA1
          JSR  LBC96          COMPARE FPA0 TO FPA1
          BRA  LB33F          CHECK TRUTH OF RELATIONAL COMPARISON

* RELATIONAL COMPARISON OF STRINGS
LB309     CLR  VALTYP         SET VARIABLE TYPE TO NUMERIC
          DEC  TRELFL         REMOVE STRING TYPE FLAG (BIT0=1 FOR STRINGS) FROM THE
*                             DESIRED RELATIONAL COMPARISON DATA
          JSR  LB657          GET LENGTH AND ADDRESS OF STRING WHOSE
*                             DESCRIPTOR ADDRESS IS IN THE BOTTOM OF FPA0
          STB  STRDES         * SAVE LENGTH AND ADDRESS IN TEMPORARY
          STX  STRDES+2       * DESCRIPTOR (STRING B)
          LDX  FPA1+2         = RETURN LENGTH AND ADDRESS OF STRING
          JSR  LB659          = WHOSE DESCRIPTOR ADDRESS IS STORED IN FPA1+2
          LDA  STRDES         LOAD ACCA WITH LENGTH OF STRING B
          PSHS B              SAVE LENGTH A ON STACK
          SUBA ,S+            SUBTRACT LENGTH A FROM LENGTH B
          BEQ  LB328          BRANCH IF STRINGS OF EQUAL LENGTH
          LDA  #1             TRUE FLAG
          BCC  LB328          TRUE IF LENGTH B > LENGTH A
          LDB  STRDES         LOAD ACCB WITH LENGTH B
          NEGA                SET FLAG = FALSE (1FF)
LB328     STA  FP0SGN         SAVE TRUE/FALSE FLAG
          LDU  STRDES+2       POINT U TO START OF STRING
          INCB                COMPENSATE FOR THE DECB BELOW
* ENTER WITH ACCB CONTAINING LENGTH OF SHORTER STRING
LB32D     DECB                DECREMENT SHORTER STRING LENGTH
          BNE  LB334          BRANCH IF ALL OF STRING NOT COMPARED
          LDB  FP0SGN         GET TRUE/FALSE FLAB
          BRA  LB33F          CHECK TRUTH OF RELATIONAL COMPARISON
LB334     LDA  ,X+            GET A BYTE FROM STRING A
          CMPA ,U+            COMPARE TO STRING B
          BEQ  LB32D          CHECK ANOTHER CHARACTER IF =
          LDB  #$FF           FALSE FLAG IF STRING A > B
          BCC  LB33F          BRANCH IF STRING A > STRING B
          NEGB                SET FLAG = TRUE

* DETERMINE TRUTH OF COMPARISON - RETURN RESULT IN FPA0
LB33F     ADDB #1             CONVERT $FF,0,1 TO 0,1,2
          ROLB                NOW IT'S 1,2,4 FOR > = <
          ANDB RELFLG         'AND' THE ACTUAL COMPARISON WITH THE DESIRED -
COMPARISON
          BEQ  LB348          BRANCH IF FALSE (NO MATCHING BITS)
          LDB  #$FF           TRUE FLAG
LB348     JMP  LBC7C          CONVERT ACCB INTO FP NUMBER IN FPA0

* DIM
LB34B     JSR  LB26D          SYNTAX CHECK FOR COMMA
DIM       LDB  #1             DIMENSION FLAG
          BSR  LB35A          SAVE ARRAY SPACE FOR THIS VARIABLE
          JSR  GETCCH         GET CURRENT INPUT CHARACTER
          BNE  LB34B          KEEP DIMENSIONING IF NOT END OF LINE
          RTS
* EVALUATE A VARIABLE - RETURN X AND
* VARPTR POINTING TO VARIABLE DESCRIPTOR
* EACH VARIABLE REQUIRES 7 BYTES - THE FIRST TWO
* BYTES ARE THE VARIABLE NAME AND THE NEXT 5
* BYTES ARE THE DESCRIPTOR. IF BIT 7 OF THE
* FIRST BYTE OF VARlABLE NAME IS SET, THE
* VARIABLE IS A DEF FN VARIABLE. IF BIT 7 OF
* THE SECOND BYTE OF VARIABLE NAME IS SET, THE
* VARIABLE IS A STRING, OTHERWISE THE VARIABLE
* IS NUMERIC.
* IF THE VARIABLE IS NOT FOUND, A ZERO VARIABLE IS
* INSERTED INTO THE VARIABLE SPACE
LB357     CLRB                DIMENSION FLAG = 0; DO NOT SET UP AN ARRAY
          JSR  GETCCH         GET CURRENT INPUT CHARACTER
LB35A     STB  DIMFLG         SAVE ARRAY FLAG
* ENTRY POINT FOR DEF FN VARIABLE SEARCH
LB35C     STA  VARNAM         SAVE INPUT CHARACTER
          JSR  GETCCH         GET CURRENT INPUT CHARACTER
          BSR  LB3A2          SET CARRY IF NOT ALPHA
          LBCS LB277          SYNTAX ERROR IF NOT ALPHA
          CLRB                DEFAULT 2ND VARIABLE CHARACTER TO ZERO
          STB  VALTYP         SET VARIABLE TYPE TO NUMERIC
          JSR  GETNCH         GET ANOTHER CHARACTER FROM BASIC
          BCS  LB371          BRANCH IF NUMERIC (2ND CHARACTER IN
*                             VARIABLE MAY BE NUMERIC)
          BSR  LB3A2          SET CARRY IF NOT ALPHA
          BCS  LB37B          BRANCH IF NOT ALPHA
LB371     TFR  A,B            SAVE 2ND CHARACTER IN ACCB
* READ INPUT CHARACTERS UNTIL A NON ALPHA OR
* NON NUMERIC IS FOUND - IGNORE ALL CHARACTERS
* IN VARIABLE NAME AFTER THE 1ST TWO
LB373     JSR  GETNCH         GET AN INPUT CHARACTER
          BCS  LB373          BRANCH IF NUMERIC
          BSR  LB3A2          SET CARRY IF NOT ALPHA
          BCC  LB373          BRANCH IF ALPHA
LB37B     CMPA #'$            CHECK FOR A STRING VARIABLE
          BNE  LB385          BRANCH IF IT IS NOT A STRING
          COM  VALTYP         SET VARIABLE TYPE TO STRING
          ADDB #$80           SET BIT 7 OF 2ND CHARACTER (STRING)
          JSR  GETNCH         GET AN INPUT CHARACTER
LB385     STB  VARNAM+1       SAVE 2ND CHARACTER IN VARNAM+1
          ORA  ARYDIS         OR IN THE ARRAY DISABLE FLAG - IF = $80,
*              DON’T SEARCH FOR VARIABLES IN THE ARRAYS
          SUBA #'(            IS THIS AN ARRAY VARIABLE?
          LBEQ LB404          BRANCH IF IT IS
          CLR  ARYDIS         RESET THE ARRAY DISABLE FLAG
          LDX  VARTAB         POINT X TO THE START OF VARIABLES
          LDD  VARNAM         GET VARIABLE IN QUESTION
LB395     CMPX ARYTAB         COMPARE X TO THE END OF VARIABLES
          BEQ  LB3AB          BRANCH IF END OF VARIABLES
          CMPD ,X++           * COMPARE VARIABLE IN QUESTION TO CURRENT
          BEQ  LB3DC          * VARIABLE AND BRANCH IF MATCH
          LEAX 5,X            = MOVE POINTER TO NEXT VARIABLE AND
          BRA  LB395          = KEEP LOOKING

* SET CARRY IF NOT UPPER CASE ALPHA
LB3A2     CMPA #'A            * CARRY SET IF < 'A'
          BCS  LB3AA          *
          SUBA #'Z+1          =
*         SUBA #-('Z+1)       = CARRY CLEAR IF <= 'Z'
          FCB  $80,$A5
LB3AA     RTS
* PUT A NEW VARIABLE IN TABLE OF VARIABLES
LB3AB     LDX  #ZERO          POINT X TO ZERO LOCATION
          LDU  ,S             GET CURRENT RETURN ADDRESS
          CMPU #LB287         DID WE COME FROM 'EVALUATE ALPHA EXPR'?
          BEQ  LB3DE          YES - RETURN A ZERO VALUE
          LDD  ARYEND         * GET END OF ARRAYS ADDRESS AND
          STD  V43            * SAVE IT AT V43
          ADDD #7             = ADD 7 TO END OF ARRAYS (EACH
          STD  V41            = VARIABLE = 7 BYTES) AND SAVE AT V41
          LDX  ARYTAB         * GET END OF VARIABLES AND SAVE AT V47
          STX  V47            *
          JSR  LAC1E          MAKE A SEVEN BYTE SLOT FOR NEW VARIABLE AT
*         TOP  OF VARIABLES
          LDX  V41            = GET NEW END OF ARRAYS AND SAVE IT
          STX  ARYEND         =
          LDX  V45            * GET NEW END OF VARIABLES AND SAVE IT
          STX  ARYTAB         *
          LDX  V47            GET OLD END OF VARIABLES
          LDD  VARNAM         GET NEW VARIABLE NAME
          STD  ,X++           SAVE VARIABLE NAME
          CLRA                * ZERO OUT THE FP VALUE OF THE NUMERIC
          CLRB                * VARIABLE OR THE LENGTH AND ADDRESS
          STD  ,X             * OF A STRING VARIABLE
          STD  2,X            *
          STA  4,X            *
LB3DC     STX  VARPTR         STORE ADDRESS OF VARIABLE VALUE
LB3DE     RTS
*
LB3DF     FCB  $90,$80,$00,$00,$00 * FLOATING POINT -32768
*                             SMALLEST SIGNED TWO BYTE INTEGER
*
LB3E4     JSR  GETNCH         GET AN INPUT CHARACTER FROM BASIC
LB3E6     JSR  LB141          GO EVALUATE NUMERIC EXPRESSION
LB3E9     LDA  FP0SGN         GET FPA0 MANTISSA SIGN
          BMI  LB44A          'FC' ERROR IF NEGATIVE NUMBER


INTCNV    JSR  LB143          'TM' ERROR IF STRING VARIABLE
          LDA  FP0EXP         GET FPA0 EXPONENT
          CMPA #$90           * COMPARE TO 32768 - LARGEST INTEGER EXPONENT AND
          BCS  LB3FE          * BRANCH IF FPA0 < 32768
          LDX  #LB3DF         POINT X TO FP VALUE OF -32768
          JSR  LBC96          COMPARE -32768 TO FPA0
          BNE  LB44A          'FC' ERROR IF NOT =
LB3FE     JSR  LBCC8          CONVERT FPA0 TO A TWO BYTE INTEGER
          LDD  FPA0+2         GET THE INTEGER
          RTS
* EVALUATE AN ARRAY VARIABLE
LB404     LDD  DIMFLG         GET ARRAY FLAG AND VARIABLE TYPE
          PSHS B,A            SAVE THEM ON STACK
          NOP                 DEAD SPACE CAUSED BY 1.2 REVISION
          CLRB                RESET DIMENSION COUNTER
LB40A     LDX  VARNAM         GET VARIABLE NAME
          PSHS X,B            SAVE VARIABLE NAME AND DIMENSION COUNTER
          BSR  LB3E4          EVALUATE EXPRESSION (DIMENSlON LENGTH)
          PULS B,X,Y          PULL OFF VARIABLE NAME, DIMENSlON COUNTER,
*                             ARRAY FLAG
          STX  VARNAM         SAVE VARIABLE NAME AND VARIABLE TYPE
          LDU  FPA0+2         GET DIMENSION LENGTH
          PSHS U,Y            SAVE DIMENSION LENGTH, ARRAY FLAG, VARIABLE TYPE
          INCB                INCREASE DIMENSION COUNTER
          JSR  GETCCH         GET CURRENT INPUT CHARACTER
          CMPA #',            CHECK FOR ANOTHER DIMENSION
          BEQ  LB40A          BRANCH IF MORE
          STB  TMPLOC         SAVE DIMENSION COUNTER
          JSR  LB267          SYNTAX CHECK FOR A ')'
          PULS A,B            * RESTORE VARIABLE TYPE AND ARRAY
          STD  DIMFLG         * FLAG - LEAVE DIMENSION LENGTH ON STACK
          LDX  ARYTAB         GET START OF ARRAYS
LB42A     CMPX ARYEND         COMPARE TO END OF ARRAYS
          BEQ  LB44F          BRANCH IF NO MATCH FOUND
          LDD  VARNAM         GET VARIABLE IN QUESTION
          CMPD ,X             COMPARE TO CURRENT VARIABLE
          BEQ  LB43B          BRANCH IF =
          LDD  2,X            GET OFFSET TO NEXT ARRAY VARIABLE
          LEAX D,X            ADD TO CURRENT POINTER
          BRA  LB42A          KEEP SEARCHING
LB43B     LDB  #2*9           'REDIMENSIONED ARRAY' ERROR
          LDA  DIMFLG         * TEST ARRAY FLAG - IF <>0 YOU ARE TRYING
          BNE  LB44C          * TO REDIMENSION AN ARRAY
          LDB  TMPLOC         GET NUMBER OF DIMENSIONS IN ARRAY
          CMPB 4,X            COMPARE TO THIS ARRAYS DIMENSIONS
          BEQ  LB4A0          BRANCH IF =
LB447     LDB  #8*2           'BAD SUBSCRIPT'
          FCB  SKP2           SKIP TWO BYTES
LB44A     LDB  #4*2           'ILLEGAL FUNCTION CALL'
LB44C     JMP  LAC46          JUMP TO ERROR SERVICING ROUTINE

* INSERT A NEW ARRAY INTO ARRAY VARIABLES
* EACH SET OF ARRAY VARIABLES IS PRECEEDED BY A DE-
* SCRIPTOR BLOCK COMPOSED OF 5+2*N BYTES WHERE N IS THE
* NUMBER OF DIMENSIONS IN THE ARRAY. THE BLOCK IS DEFINED
* AS FOLLOWS: BYTES 0,1:VARIABLE'S NAME; 2,3:TOTAL LENGTH
* OF ARRAY ITEMS AND DESCRIPTOR BLOCK; 4:NUMBER OF DIMEN-
* ISIONS; 5,6:LENGTH OF DIMENSION 1; 7,8:LENGTH OF DIMEN-
* SION 2;… 4+N,5+N:LENGTH OF DIMENSION N.

LB44F     LDD  #5             * 5 BYTES/ARRAY ENTRY SAVE AT COEFPT
          STD  COEFPT         *
          LDD  VARNAM         = GET NAME OF ARRAY AND SAVE IN
          STD  ,X             = FIRST 2 BYTES OF DESCRIPTOR
          LDB  TMPLOC         GET NUMBER OF DIMENSIONS AND SAVE IN
          STB  4,X            * 5TH BYTE OF DESCRIPTOR
          JSR  LAC33          CHECK FOR ROOM FOR DESCRIPTOR IN FREE RAM
          STX  V41            TEMPORARILY SAVE DESCRIPTOR ADDRESS
LB461     LDB  #11            * DEFAULT DIMENSION VALUE:X(10)
          CLRA                *
          TST  DIMFLG         = CHECK ARRAY FLAG AND BRANCH IF
          BEQ  LB46D          = NOT DIMENSIONING AN ARRAY
          PULS A,B            GET DIMENSION LENGTH
          ADDD #1             ADD ONE (X(0) HAS A LENGTH OF ONE)
LB46D     STD  5,X            SAVE LENGTH OF ARRAY DIMENSION
          BSR  LB4CE          MULTIPLY ACCUM ARRAY SIZE NUMBER LENGTH
*                             OF NEW DIMENSION
          STD  COEFPT         TEMP STORE NEW CURRENT ACCUMULATED ARRAY SIZE
          LEAX 2,X            BUMP POINTER UP TWO
          DEC  TMPLOC         * DECREMENT DIMENSION COUNTER AND BRANCH IF
          BNE  LB461          * NOT DONE WITH ALL DIMENSIONS
          STX  TEMPTR         SAVE ADDRESS OF (END OF ARRAY DESCRIPTOR - 5)
          ADDD TEMPTR         ADD TOTAL SIZE OF NEW ARRAY
          LBCS LAC44          'OM' ERROR IF > $FFFF
          TFR  D,X            SAVE END OF ARRAY IN X
          JSR  LAC37          MAKE SURE THERE IS ENOUGH FREE RAM FOR ARRAY
          SUBD #STKBUF-5      SUBTRACT OUT THE (STACK BUFFER - 5)
          STD  ARYEND         SAVE NEW END OF ARRAYS
          CLRA                ZERO = TERMINATOR BYTE
LB48C     LEAX -1,X           * STORE TWO TERMINATOR BYTES AT
          STA  5,X            * THE END OF THE ARRAY DESCRIPTOR
          CMPX TEMPTR         *
          BNE  LB48C          *
          LDX  V41            GET ADDRESS OF START OF DESCRIPTOR
          LDA  ARYEND         GET MSB OF END OF ARRAYS; LSB ALREADY THERE
          SUBD V41            SUBTRACT OUT ADDRESS OF START OF DESCRIPTOR
          STD  2,X            SAVE LENGTH OF (ARRAY AND DESCRIPTOR)
          LDA  DIMFLG         * GET ARRAY FLAG AND BRANCH
          BNE  LB4CD          * BACK IF DIMENSIONING
* CALCULATE POINTER TO CORRECT ELEMENT
LB4A0     LDB  4,X            GET THE NUMBER OF DIMENSIONS
          STB  TMPLOC         TEMPORARILY SAVE
          CLRA                * INITIALIZE POINTER
          CLRB                * TO ZERO
LB4A6     STD  COEFPT         SAVE ACCUMULATED POINTER
          PULS A,B            * PULL DIMENSION ARGUMENT OFF THE
          STD  FPA0+2         * STACK AND SAVE IT
          CMPD 5,X            COMPARE TO STORED 'DIM' ARGUMENT
          BCC  LB4EB          'BS' ERROR IF > = 'DIM' ARGUMENT
          LDU  COEFPT         * GET ACCUMULATED POINTER AND
          BEQ  LB4B9          * BRANCH IF 1ST DIMENSION
          BSR  LB4CE          = MULTIPLY ACCUMULATED POINTER AND DIMENSION
          ADDD FPA0+2         = LENGTH AND ADD TO CURRENT ARGUMENT
LB4B9     LEAX 2,X            MOVE POINTER TO NEXT DIMENSION
          DEC  TMPLOC         * DECREMENT DIMENSION COUNTER AND
          BNE  LB4A6          * BRANCH IF ANY DIMENSIONS LEFT
* MULTIPLY ACCD BY 5 - 5 BYTES/ARRAY VALUE
          STD  ,--S
          ASLB
          ROLA                TIMES 2
          ASLB
          ROLA                TIMES 4
          ADDD ,S++           TIMES 5
          LEAX D,X            ADD OFFSET TO START OF ARRAY
          LEAX 5,X            ADJUST POINTER FOR SIZE OF DESCRIPTOR
          STX  VARPTR         SAVE POINTER TO ARRAY VALUE
LB4CD     RTS
* MULTIPLY 2 BYTE NUMBER IN 5,X BY THE 2 BYTE NUMBER
* IN COEFPT. RETURN RESULT IN ACCD, BS ERROR IF > $FFFF
LB4CE     LDA  #16            16 SHIFTS TO DO A MULTIPLY
          STA  V45            SHIFT COUNTER
          LDD  5,X            * GET SIZE OF DIMENSION
          STD  BOTSTK         * AND SAVE IT
          CLRA                * ZERO
          CLRB                * ACCD
LB4D8     ASLB                = SHIFT ACCB LEFT
          ROLA                = ONE BIT
          BCS  LB4EB          BS' ERROR IF CARRY
          ASL  COEFPT+1       * SHIFT MULTIPLICAND LEFT ONE
          ROL  COEFPT         * BIT - ADD MULTIPLIER TO ACCUMULATOR
          BCC  LB4E6          * IF CARRY <> 0
          ADDD BOTSTK         ADD MULTIPLIER TO ACCD
          BCS  LB4EB          BS' ERROR IF CARRY (>$FFFF)
LB4E6     DEC  V45            * DECREMENT SHIFT COUNTER
          BNE  LB4D8          * IF NOT DONE
          RTS
LB4EB     JMP  LB447          BS' ERROR
*
* MEM
* THIS IS NOT A TRUE INDICATOR OF FREE MEMORY BECAUSE
* BASIC REQUIRES A STKBUF SIZE BUFFER FOR THE STACK
* FOR WHICH MEM DOES NOT ALLOW.
*
MEM       TFR  S,D            PUT STACK POINTER INTO ACCD
          SUBD ARYEND         SUBTRACT END OF ARRAYS
          FCB  SKP1           SKIP ONE BYTE
*CONVERT THE VALUE IN ACCB INTO A FP NUMBER IN FPA0
LB4F3     CLRA                CLEAR MS BYTE OF ACCD
* CONVERT THE VALUE IN ACCD INTO A FLOATING POINT NUMBER IN FPA0
GIVABF    CLR  VALTYP         SET VARIABLE TYPE TO NUMERIC
          STD  FPA0           SAVE ACCD IN TOP OF FACA
          LDB  #$90           EXPONENT REQUIRED IF THE TOP TWO BYTES
*         OF   FPA0 ARE TO BE TREATED AS AN INTEGER IN FPA0
          JMP  LBC82          CONVERT THE REST OF FPA0 TO AN INTEGER

* STR$
STR       JSR  LB143          TM' ERROR IF STRING VARIABLE
          LDU  #STRBUF+2      *CONVERT FP NUMBER TO ASCII STRING IN
          JSR  LBDDC          *THE STRING BUFFER
          LEAS 2,S            PURGE THE RETURN ADDRESS FROM THE STACK
          LDX  #STRBUF+1      *POINT X TO STRING BUFFER AND SAVE
          BRA  LB518          *THE STRING IN THE STRING SPACE
* RESERVE ACCB BYTES OF STRING SPACE. RETURN START
* ADDRESS IN (X) AND FRESPC
LB50D     STX  V4D            SAVE X IN V4D
LB50F     BSR  LB56D          RESERVE ACCB BYTES IN STRING SPACE
LB511     STX  STRDES+2       SAVE NEW STRING ADDRESS
          STB  STRDES         SAVE LENGTH OF RESERVED BLOCK
          RTS
LB516     LEAX -1,X           MOVE POINTER BACK ONE
* SCAN A LINE FROM (X) UNTIL AN END OF LINE FLAG (ZERO) OR
* EITHER OF THE TWO TERMINATORS STORED IN CHARAC OR ENDCHR IS MATCHED.
* THE RESULTING STRING IS STORED IN THE STRING SPACE
* ONLY IF THE START OF THE STRING IS <= STRBUF+2
LB518     LDA  #'"            * INITIALIZE
          STA  CHARAC         * TERMINATORS
LB51A     STA  ENDCHR         * TO "
LB51E     LEAX 1,X            MOVE POINTER UP ONE
          STX  RESSGN         TEMPORARILY SAVE START OF STRING
          STX  STRDES+2       SAVE START OF STRING IN TEMP DESCRIPTOR
          LDB  #-1            INITIALIZE CHARACTER COUNTER TO - 1
LB526     INCB                INCREMENT CHARACTER COUNTER
          LDA  ,X+            GET CHARACTER
          BEQ  LB537          BRANCH IF END OF LINE
          CMPA CHARAC         * CHECK FOR TERMINATORS
          BEQ  LB533          * IN CHARAC AND ENDCHR
          CMPA ENDCHR         * DON'T MOVE POINTER BACK
          BNE  LB526          * ONE IF TERMINATOR IS "MATCHED"
LB533     CMPA #'"            = COMPARE CHARACTER TO STRING DELIMITER: "
          BEQ  LB539          = & DON'T MOVE POINTER BACK IF SO
LB537     LEAX -1,X           MOVE POINTER BACK ONE
LB539     STX  COEFPT         SAVE END OF STRING ADDRESS
          STB  STRDES         SAVE STRING LENGTH IN TEMP DESCRIPTOR
          LDU  RESSGN         GET INITlAL STRING START
          CMPU #STRBUF+2      COMPARE TO START OF STRING BUFFER
LB543     BHI  LB54C          BRANCH IF > START OF STRING BUFFER
          BSR  LB50D          GO RESERVE SPACE FOR THE STRING
          LDX  RESSGN         POINT X TO THE BEGINNING OF THE STRING
          JSR  LB645          MOVE (B) BYTES FROM (X) TO
*                             [FRESPC] - MOVE STRING DATA
* PUT DIRECT PAGE STRING DESCRIPTOR BUFFER DATA
* ON THE STRING STACK. SET VARIABLE TYPE TO STRING
LB54C     LDX  TEMPPT         GET NEXT AVAILABLE STRING STACK DESCRIPTOR
          CMPX #LINHDR        COMPARE TO TOP OF STRING DESCRIPTOR STACK - WAS #CFNBUF
          BNE  LB558          FORMULA O.K.
          LDB  #15*2          STRING FORMULA TOO COMPLEX' ERROR
LB555     JMP  LAC46          JUMP TO ERROR SERVICING ROUTINE
LB558     LDA  STRDES         * GET LENGTH OF STRING AND SAVE IT
*         STA  ,X             * IN BYTE 0 OF DESCRIPTOR
          FCB  $A7,$00
          LDD  STRDES+2       = GET START ADDRESS OF ACTUAL STRING
          STD  2,X            = AND SAVE IN BYTES 2,3 OF DESCRIPTOR
          LDA  #$FF           * VARIABLE TYPE = STRING
          STA  VALTYP         * SAVE IN VARIABLE TYPE FLAG
          STX  LASTPT         = SAVE START OF DESCRIPTOR
          STX  FPA0+2         = ADDRESS IN LASTPT AND FPA0
          LEAX 5,X            5 BYTES/STRING DESCRIPTOR
          STX  TEMPPT         NEXT AVAILABLE STRING VARIABLE DESCRIPTOR
          RTS
* RESERVE ACCB BYTES IN STRING STORAGE SPACE
* RETURN WITH THE STARTING ADDRESS OF THE
* RESERVED STRING SPACE IN (X) AND FRESPC
LB56D     CLR  GARBFL         CLEAR STRING REORGANIZATION FLAG
LB56F     CLRA                * PUSH THE LENGTH OF THE
          PSHS B,A            * STRING ONTO THE STACK
          LDD  STRTAB         GET START OF STRING VARIABLES
          SUBD ,S+            SUBTRACT STRING LENGTH
          CMPD FRETOP         COMPARE TO START OF STRING STORAGE
          BCS  LB585          IF BELOW START, THEN REORGANIZE
          STD  STRTAB         SAVE NEW START OF STRING VARIABLES
          LDX  STRTAB         GET START OF STRING VARIABLES
          LEAX 1,X            ADD ONE
          STX  FRESPC         SAVE START ADDRESS OF NEWLY RESERVED SPACE
          PULS B,PC           RESTORE NUMBER OF BYTES RESERVED AND RETURN
LB585     LDB  #2*13          OUT OF STRING SPACE' ERROR
          COM  GARBFL         TOGGLE REORGANIZATiON FLAG
          BEQ  LB555          ERROR IF FRESHLY REORGANIZED
          BSR  LB591          GO REORGANIZE STRING SPACE
          PULS B              GET BACK THE NUMBER OF BYTES TO RESERVE
          BRA  LB56F          TRY TO RESERVE ACCB BYTES AGAIN
* REORGANIZE THE STRING SPACE
LB591     LDX  MEMSIZ         GET THE TOP OF STRING SPACE
LB593     STX  STRTAB         SAVE TOP OF UNORGANIZED STRING SPACE
          CLRA                * ZERO OUT ACCD
          CLRB                * AND RESET VARIABLE
          STD  V4B            * POINTER TO 0
          LDX  FRETOP         POINT X TO START OF STRING SPACE
          STX  V47            SAVE POINTER IN V47
          LDX  #STRSTK        POINT X TO START OF STRING DESCRIPTOR STACK
LB5A0     CMPX TEMPPT         COMPARE TO ADDRESS OF NEXT AVAILABLE DESCRIPTOR
          BEQ  LB5A8          BRANCH IF TOP OF STRING STACK
          BSR  LB5D8          CHECK FOR STRING IN UNORGANIZED STRING SPACE
          BRA  LB5A0          KEEP CHECKING
LB5A8     LDX  VARTAB         GET THE END OF BASIC PROGRAM
LB5AA     CMPX ARYTAB         COMPARE TO END OF VARIABLES
          BEQ  LB5B2          BRANCH IF AT TOP OF VARIABLES
          BSR  LB5D2          CHECK FOR STRING IN UNORGANIZED STRING SPACE
          BRA  LB5AA          KEEP CHECKING VARIABLES
LB5B2     STX  V41            SAVE ADDRESS OF THE END OF VARIABLES
LB5B4     LDX  V41            GET CURRENT ARRAY POINTER
LB5B6     CMPX ARYEND         COMPARE TO THE END OF ARRAYS
          BEQ  LB5EF          BRANCH IF AT END OF ARRAYS
          LDD  2,X            GET LENGTH OF ARRAY AND DESCRIPTOR
          ADDD V41            * ADD TO CURRENT ARRAY POINTER
          STD  V41            * AND SAVE IT
          LDA  1,X            GET 1ST CHARACTER OF VARIABLE NAME
          BPL  LB5B4          BRANCH IF NUMERIC ARRAY
          LDB  4,X            GET THE NUMBER OF DIMENSIONS IN THIS ARRAY
          ASLB                MULTIPLY BY 2
          ADDB #5             ADD FIVE BYTES (VARIABLE NAME, ARRAY
*                             LENGTH, NUMBER DIMENSIONS)
          ABX                 X NOW POINTS TO START OF ARRAY ELEMENTS
LB5CA     CMPX V41            AT END OF THIS ARRAY?
          BEQ  LB5B6          YES - CHECK FOR ANOTHER
          BSR  LB5D8          CHECK FOR STRING LOCATED IN
*                             UNORGANIZED STRING SPACE
          BRA  LB5CA          KEEP CHECKING ELEMENTS IN THIS ARRAY
LB5D2     LDA  1,X            GET F1RST BYTE OF VARIABLE NAME
          LEAX 2,X            MOVE POINTER TO DESCRIPTOR
          BPL  LB5EC          BRANCH IF VARIABLE IS NUMERIC
* SEARCH FOR STRING - ENTER WITH X POINTING TO
* THE STRING DESCRIPTOR. IF STRING IS STORED
* BETWEEN V47 AND STRTAB, SAVE DESCRIPTOR POINTER
* IN V4B AND RESET V47 TO STRING ADDRESS
LB5D8     LDB  ,X             GET THE LENGTH OF THE STRING
          BEQ  LB5EC          BRANCH IF NULL - NO STRING
          LDD  2,X            GET STARTING ADDRESS OF THE STRING
          CMPD STRTAB         COMPARE TO THE START OF STRING VARIABLES
          BHI  LB5EC          BRANCH IF THIS STRING IS STORED IN
*              THE STRING VARIABLES
          CMPD V47            COMPARE TO START OF STRING SPACE
          BLS  LB5EC          BRANCH IF NOT STORED IN THE STRING SPACE
          STX  V4B            SAVE VARIABLE POINTER IF STORED IN STRING SPACE
          STD  V47            SAVE STRING STARTING ADDRESS
LB5EC     LEAX 5,X            MOVE TO NEXT VARIABLE DESCRIPTOR
LB5EE     RTS
LB5EF     LDX  V4B            GET ADDRESS OF THE DESCRIPTOR FOR THE
*              STRING WHICH IS STORED IN THE HIGHEST RAM ADDRESS IN
*              THE UNORGANIZED STRING SPACE
          BEQ  LB5EE          BRANCH IF NONE FOUND AND REORGANIZATION DONE
          CLRA                CLEAR MS BYTE OF LENGTH
          LDB  ,X             GET LENGTH OF STRING
          DECB                SUBTRACT ONE
          ADDD V47            ADD LENGTH OF STRING TO ITS STARTING ADDRESS
          STD  V43            SAVE AS MOVE STARTING ADDRESS
          LDX  STRTAB         POINT X TO THE START OF ORGANIZED STRING VARIABLES
          STX  V41            SAVE AS MOVE ENDING ADDRESS
          JSR  LAC20          MOVE STRING FROM CURRENT POSITION TO THE
*              TOP OF UNORGANIZED STRING SPACE
          LDX  V4B            POINT X TO STRING DESCRIPTOR
          LDD  V45            * GET NEW STARTING ADDRESS OF STRING AND
          STD  2,X            * SAVE IT IN DESCRIPTOR
          LDX  V45            GET NEW TOP OF UNORGANIZED STRING SPACE
          LEAX -1,X           MOVE POINTER BACK ONE
          JMP  LB593          JUMP BACK AND REORGANIZE SOME MORE


LB60F     LDD  FPA0+2         * GET DESCRIPTOR ADDRESS OF STRING A
          PSHS B,A            * AND SAVE IT ON THE STACK
          JSR  LB223          GET DESCRIPTOR ADDRESS OF STRING B
          JSR  LB146          TM' ERROR IF NUMERIC VARIABLE
          PULS X              * POINT X TO STRING A DESCRIPTOR
          STX  RESSGN         * ADDRESS AND SAVE IT IN RESSGN
          LDB  ,X             GET LENGTH OF STRING A
          LDX  FPA0+2         POINT X TO DESCRIPTOR OF STRING B
          ADDB ,X             ADD LENGTH OF STRING B TO STR1NG A
          BCC  LB62A          BRANCH IF LENGTH < 256
          LDB  #2*14          STRING TOO LONG' ERROR IF LENGTH > 255
          JMP  LAC46          JUMP TO ERROR SERVICING ROUTINE
LB62A     JSR  LB50D          RESERVE ROOM IN STRING SPACE FOR NEW STRING
          LDX  RESSGN         GET DESCRIPTOR ADDRESS OF STRING A
          LDB  ,X             GET LENGTH OF STRING A
          BSR  LB643          MOVE STRING A INTO RESERVED BUFFER IN STRING SPACE
          LDX  V4D            GET DESCRIPTOR ADDRESS OF STRING B
          BSR  LB659          GET LENGTH AND ADDRESS OF STRING B
          BSR  LB645          MOVE STRING B INTO REST OF RESERVED BUFFER
          LDX  RESSGN         POINT X TO DESCRIPTOR OF STRING A
          BSR  LB659          DELETE STRING A IF LAST STRING ON STRING STACK
          JSR  LB54C          PUT STRING DESCRIPTOR ON THE STRING STACK
          JMP  LB168          BRANCH BACK TO EXPRESSION EVALUATION

* MOVE (B) BYTES FROM 2,X TO FRESPC
LB643     LDX  2,X            POINT X TO SOURCE ADDRESS
LB645     LDU  FRESPC         POINT U TO DESTINATION ADDRESS
          INCB                COMPENSATION FOR THE DECB BELOW
          BRA  LB64E          GO MOVE THE BYTES
* MOVE B BYTES FROM (X) TO (U)
LB64A     LDA  ,X+            * GET A SOURCE BYTE AND MOVE IT
          STA  ,U+            * TO THE DESTINATION
LB64E     DECB                DECREMENT BYTE COUNTER
          BNE  LB64A          BRANCH IF ALL BYTES NOT MOVED
          STU  FRESPC         SAVE ENDING ADDRESS IN FRESPC
          RTS
* RETURN LENGTH (ACCB) AND ADDRESS (X) OF
* STRING WHOSE DESCRIPTOR IS IN FPA0+2
* DELETE THE STRING IF IT IS THE LAST ONE
* PUT ON THE STRING STACK. REMOVE STRING FROM STRING
* SPACE IF IT IS AT THE BOTTOM OF STRING VARIABLES.
LB654     JSR  LB146          TM' ERROR IF VARIABLE TYPE = NUMERIC
LB657     LDX  FPA0+2         GET ADDRESS OF SELECTED STRING DESCRIPTOR
LB659     LDB  ,X             GET LENGTH OF STRING
          BSR  LB675          * CHECK TO SEE IF THIS STRING DESCRIPTOR WAS
          BNE  LB672          * THE LAST ONE PUT ON THE STRING STACK AND
*                             * BRANCH IF NOT
          LDX  5+2,X          GET START ADDRESS OF STRING JUST REMOVED
          LEAX -1,X           MOVE POINTER DOWN ONE
          CMPX STRTAB         COMPARE TO START OF STRING VARIABLES
          BNE  LB66F          BRANCH IF THIS STRING IS NOT AT THE BOTTOM
*                             OF STRING VARIABLES
          PSHS B              SAVE LENGTH; ACCA WAS CLEARED
          ADDD STRTAB         * ADD THE LENGTH OF THE JUST REMOVED STRING
          STD  STRTAB         * TO THE START OF STRING VARIABLES - THIS WILL
*                             * REMOVE THE STRING FROM THE STRING SPACE
          PULS B              RESTORE LENGTH
LB66F     LEAX 1,X            ADD ONE TO POINTER
          RTS
LB672     LDX  2,X            *POINT X TO ADDRESS OF STRING NOT
          RTS                 *ON THE STRING STACK
* REMOVE STRING FROM STRING STACK. ENTER WITH X
* POINTING TO A STRING DESCRIPTOR - DELETE THE
* STRING FROM STACK IF IT IS ON TOP OF THE
* STACK. IF THE STRING IS DELETED, SET THE ZERO FLAG
LB675     CMPX LASTPT         *COMPARE TO LAST USED DESCRIPTOR ADDRESS
          BNE  LB680          *ON THE STRING STACK, RETURN IF DESCRIPTOR
*                             *ADDRESS NOT ON THE STRING STACK
          STX  TEMPPT         SAVE LAST USED DESCRIPTOR AS NEXT AVAILABLE
          LEAX -5,X           * MOVE LAST USED DESCRIPTOR BACK 5 BYTES
          STX  LASTPT         * AND SAVE AS THE LAST USED DESCRIPTOR ADDR
          CLRA                SET ZERO FLAG
LB680     RTS

* LEN
LEN       BSR  LB686          POINT X TO PROPER STRING AND GET LENGTH
LB683     JMP  LB4F3          CONVERT ACCB TO FP NUMBER IN FPA0
* POINT X TO STRING ADDRESS LOAD LENGTH INTO
* ACCB. ENTER WITH THE STRING DESCRIPTOR IN
* BOTTOM TWO BYTES OF FPA0
LB686     BSR  LB654          GET LENGTH AND ADDRESS OF STRING
          CLR  VALTYP         SET VARIABLE TYPE TO NUMERIC
          TSTB                SET FLAGS ACCORDING TO LENGTH
          RTS

* CHR$
CHR       JSR  LB70E          CONVERT FPA0 TO AN INTEGER IN ACCD
LB68F     LDB  #1             * RESERVE ONE BYTE IN
          JSR  LB56D          * THE STRING SPACE
          LDA  FPA0+3         GET ASCII STRING VALUE
          JSR  LB511          SAVE RESERVED STRING DESCRIPTOR IN TEMP DESCRIPTOR
          STA  ,X             SAVE THE STRING (IT'S ONLY ONE BYTE)
LB69B     LEAS 2,S            PURGE THE RETURN ADDRESS OFF OF THE STACK
LB69D     JMP  LB54C          PUT TEMP DESCRIPTOR DATA ONTO STRING STACK


ASC       BSR  LB6A4          PUT 1ST CHARACTER OF STRING INTO ACCB
          BRA  LB683          CONVERT ACCB INTO FP NUMBER IN FPA0
LB6A4     BSR  LB686          POINT X TO STRING DESCRIPTOR
          BEQ  LB706          FC' ERROR IF NULL STRING
          LDB  ,X             GET FIRST BYTE OF STRING
          RTS


LEFT      BSR  LB6F5          GET ARGUMENTS FROM STACK
LB6AD     CLRA                CLEAR STRING POINTER OFFSET - OFFSET = 0 FOR LEFT$
LB6AE     CMPB ,X             * COMPARE LENGTH PARAMETER TO LENGTH OF
          BLS  LB6B5          * STRING AND BRANCH IF LENGTH OF STRING
*                             >= LENGTH PARAMETER
          LDB  ,X             USE LENGTH OF STRING OTHERWISE
          CLRA                CLEAR STRING POINTER OFFSET (0 FOR LEFT$)
LB6B5     PSHS B,A            PUSH PARAMETERS ONTO STACK
          JSR  LB50F          RESERVE ACCB BYTES IN THE STRING SPACE
          LDX  V4D            POINT X TO STRING DESCRIPTOR
          BSR  LB659          GET ADDRESS OF OLD STRING (X=ADDRESS)
          PULS B              * PULL STRING POINTER OFFSET OFF OF THE STACK
          ABX                 * AND ADD IT TO STRING ADDRESS
          PULS B              PULL LENGTH PARAMETER OFF OF THE STACK
          JSR  LB645          MOVE ACCB BYTES FROM (X) TO [FRESPC]
          BRA  LB69D          PUT TEMP STRING DESCRIPTOR ONTO THE STRING STACK

* RIGHT$
RIGHT     BSR  LB6F5          GET ARGUMENTS FROM STACK
          SUBA ,X             ACCA=LENGTH PARAMETER - LENGTH OF OLD STRING
          NEGA                NOW ACCA = LENGTH OF OLD STRING
          BRA  LB6AE          PUT NEW STRING IN THE STRING SPACE

* MID$
MID       LDB  #$FF           * GET DEFAULT VALUE OF LENGTH AND
          STB  FPA0+3         * SAVE IT IN FPA0
          JSR  GETCCH         GET CURRENT CHARACTER FROM BASIC
          CMPA #')            ARGUMENT DELIMITER?
          BEQ  LB6DE          YES - NO LENGTH PARAMETER GIVEN
          JSR  LB26D          SYNTAX CHECK FOR COMMA
          BSR  LB70B          EVALUATE NUMERIC EXPRESSION (LENGTH)
LB6DE     BSR  LB6F5          GET ARGUMENTS FROM STACK
          BEQ  LB706          FC' ERROR IF NULL STRING
          CLRB                CLEAR LENGTH COUNTER (DEFAULT VALUE)
          DECA                *SUOTRACT ONE FROM POSITION PARAMETER (THESE
          CMPA ,X             *ROUTINES EXPECT 1ST POSITION TO BE ZERO, NOT ONE)
*                             *AND COMPARE IT TO LENGTH OF OLD STRING
          BCC  LB6B5          IF POSITION > LENGTH OF OLD STRING, THEN NEW
*                             STRING WILL BE A NULL STRING
          TFR  A,B            SAVE ABSOLUTE POSITION PARAMETER IN ACCB
          SUBB ,X             ACCB=POSITION-LENGTH OF OLD STRING
          NEGB                NOW ACCB=LENGTH OF OLDSTRING-POSITION
          CMPB FPA0+3         *IF THE AMOUNT OF OLD STRING TO THE RIGHT OF
          BLS  LB6B5          *POSITION IS <= THE LENGTH PARAMETER, BRANCH AND
* USE ALL OF THE STRING TO THE RIGHT OF THE POSITION
* INSTEAD OF THE LENGTH PARAMETER
          LDB  FPA0+3         GET LENGTH OF NEW STRING
          BRA  LB6B5          PUT NEW STRING IN STRING SPACE
* DO A SYNTAX CHECK FOR ")", THEN PULL THE PREVIOUSLY CALCULATED NUMERIC
* ARGUMENT (ACCD) AND STRING ARGUMENT DESCRIPTOR ADDR OFF OF THE STACK
LB6F5     JSR  LB267          SYNTAX CHECK FOR A ")"
          LDU  ,S             LOAD THE RETURN ADDRESS INTO U REGISTER
          LDX  5,S            * GET ADDRESS OF STRING AND
          STX  V4D            * SAVE IT IN V4D
          LDA  4,S            = PUT LENGTH OF STRING IN
          LDB  4,S            = BOTH ACCA AND ACCB
          LEAS 7,S            REMOVE DESCRIPTOR AND RETURN ADDRESS FROM STACK
          TFR  U,PC           JUMP TO ADDRESS IN U REGISTER
LB706     JMP  LB44A          ILLEGAL FUNCTION CALL'
* EVALUATE AN EXPRESSION - RETURN AN INTEGER IN
* ACCB - 'FC' ERROR IF EXPRESSION > 255
LB709     JSR  GETNCH         GET NEXT BASIC INPUT CHARACTER
LB70B     JSR  LB141          EVALUATE A NUMERIC EXPRESSION
LB70E     JSR  LB3E9          CONVERT FPA0 TO INTEGER IN ACCD
          TSTA                TEST MS BYTE OF INTEGER
          BNE  LB706          FC' ERROR IF EXPRESSION > 255
          JMP  GETCCH         GET CURRENT INPUT CHARACTER FROM BASIC

* VAL
VAL       JSR  LB686          POINT X TO STRING ADDRESS
          LBEQ LBA39          IF NULL STRING SET FPA0
          LDU  CHARAD         SAVE INPUT POINTER IN REGISTER U
          STX  CHARAD         POINT INPUT POINTER TO ADDRESS OF STRING
          ABX  MOVE POINTER TO END OF STRING TERMINATOR
          LDA  ,X             GET LAST BYTE OF STRING
          PSHS U,X,A          SAVE INPUT POINTER, STRING TERMINATOR
*         ADDRESS AND CHARACTER
          CLR  ,X             CLEAR STRING TERMINATOR : FOR ASCII - FP CONVERSION
          JSR  GETCCH         GET CURRENT CHARACTER FROM BASIC
          JSR  LBD12          CONVERT AN ASCII STRING TO FLOATING POINT
          PULS A,X,U          RESTORE CHARACTERS AND POINTERS
          STA  ,X             REPLACE STRING TERMINATOR
          STU  CHARAD         RESTORE INPUT CHARACTER
          RTS

LB734     BSR  LB73D          * EVALUATE AN EXPRESSION, RETURN
          STX  BINVAL         * THE VALUE IN X; STORE IT IN BINVAL
LB738     JSR  LB26D          SYNTAX CHECK FOR A COMMA
          BRA  LB70B          EVALUATE EXPRESSION IN RANGE 0 <= X < 256
* EVALUATE EXPRESSION : RETURN INTEGER PORTION IN X - 'FC' ERROR IF

LB73D     JSR  LB141          EVALUATE NUMERIC EXPRESSION
LB740     LDA  FP0SGN         GET SIGN OF FPA0 MANTISSA
          BMI  LB706          ILLEGAL FUNCTION CALL' IF NEGATIVE
          LDA  FP0EXP         GET EXPONENT OF FPA0
          CMPA #$90           COMPARE TO LARGEST POSITIVE INTEGER
          BHI  LB706          ILLEGAL FUNCTION CALL' IF TOO LARGE
          JSR  LBCC8          SHIFT BINARY POINT TO EXTREME RIGHT OF FPA0
          LDX  FPA0+2         LOAD X WITH LOWER TWO BYTES OF FPA0
          RTS

* PEEK
PEEK      BSR  LB740          CONVERT FPA0 TO INTEGER IN REGISTER X
          LDB  ,X             GET THE VALUE BEING 'PEEK'ED
          JMP  LB4F3          CONVERT ACCB INTO A FP NUMBER

* POKE
POKE      BSR  LB734          EVALUATE 2 EXPRESSIONS
          LDX  BINVAL         GET THE ADDRESS TO BE 'POKE'ED
          STB  ,X             STORE THE DATA IN THAT ADDRESS
          RTS
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
